grodansparadis/zeus/datasheets/capacitors.jpg

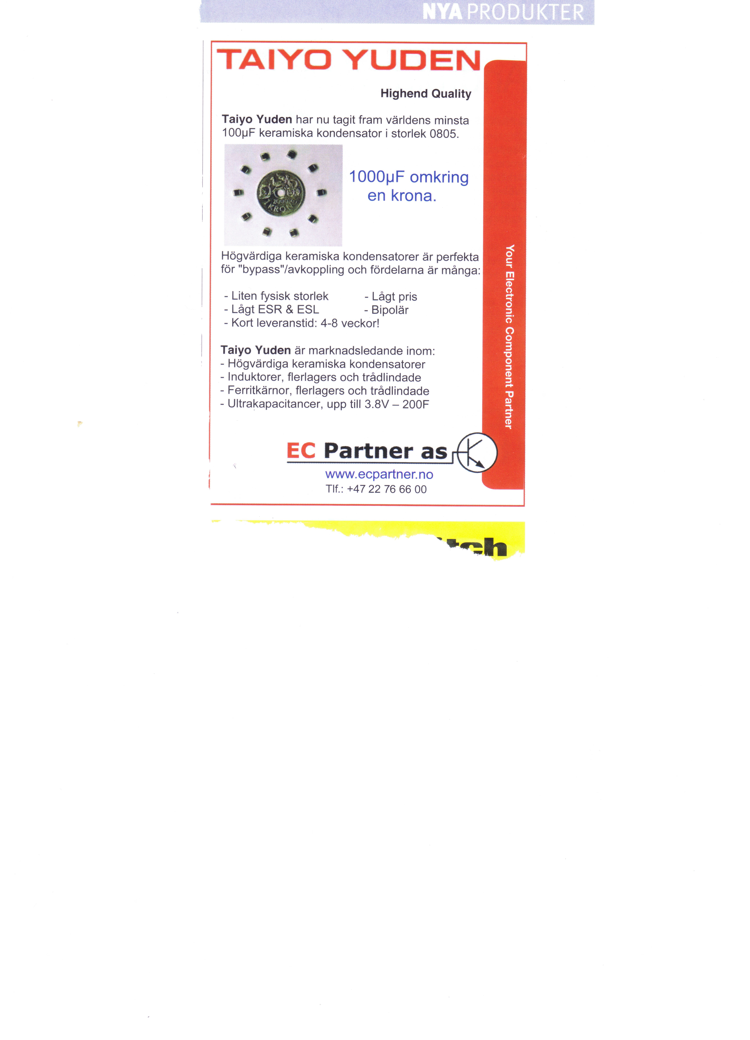
datasheets/capacitors.jpg
