grodansparadis/zeus/docs/547a1a08af27833d355dc69e661ba805.media.899x562.png

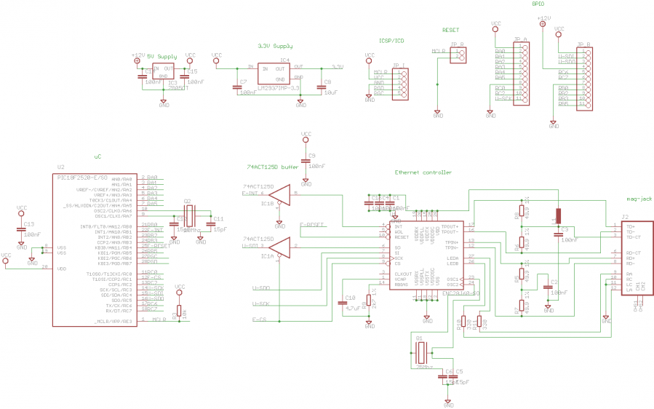
docs/547a1a08af27833d355dc69e661ba805.media.899x562.png
