grodansparadis/zeus/docs/AVR-WebServer-Rev.jpeg

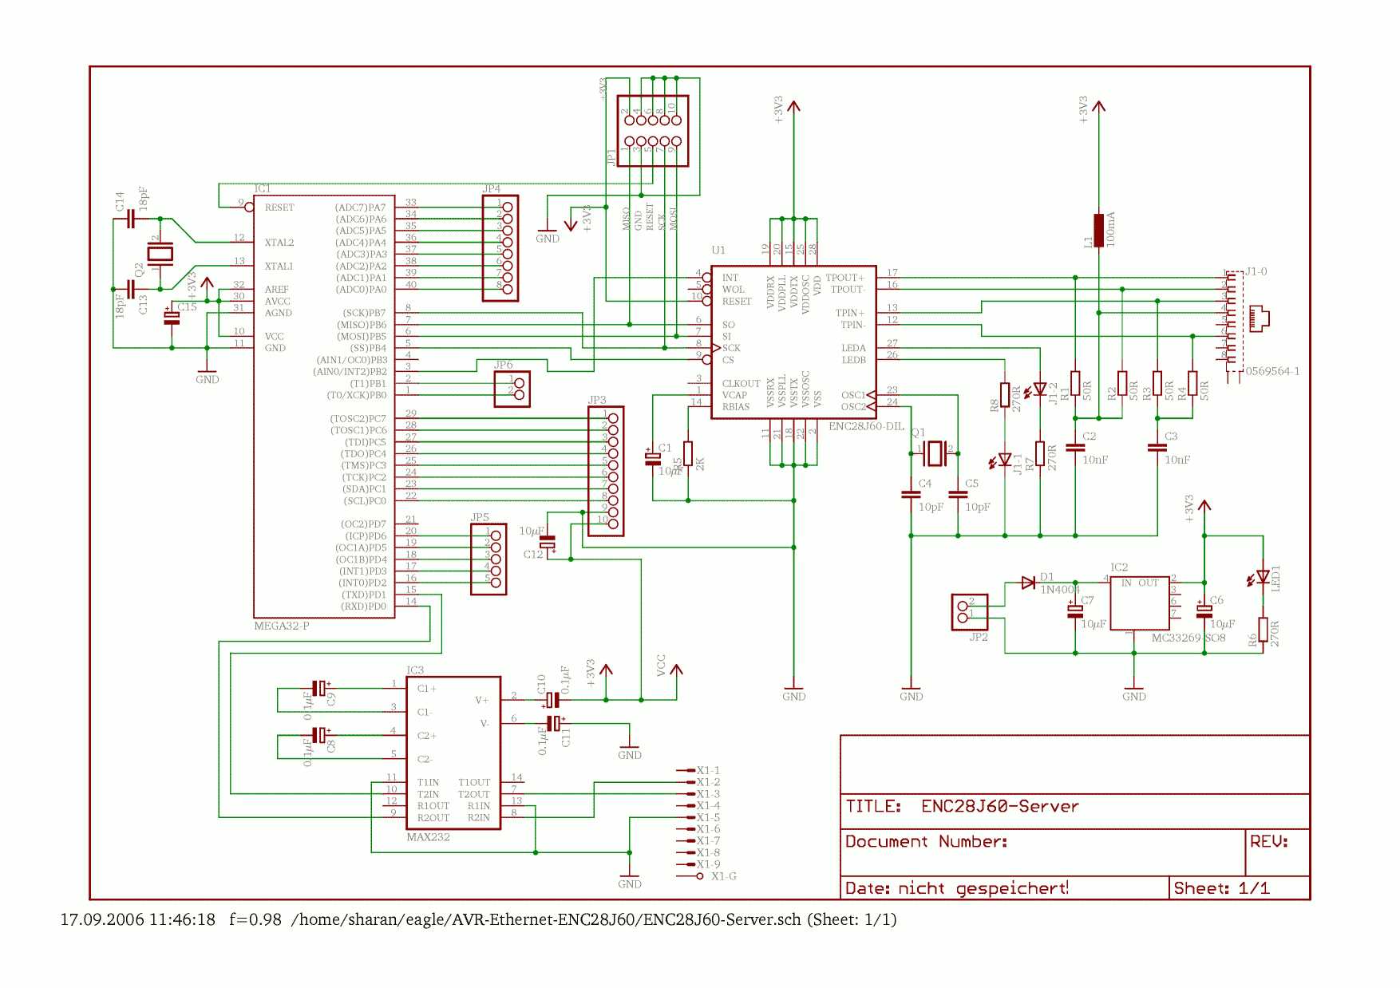
docs/AVR-WebServer-Rev.jpeg
