grodansparadis/zeus/docs/Magjack2.png

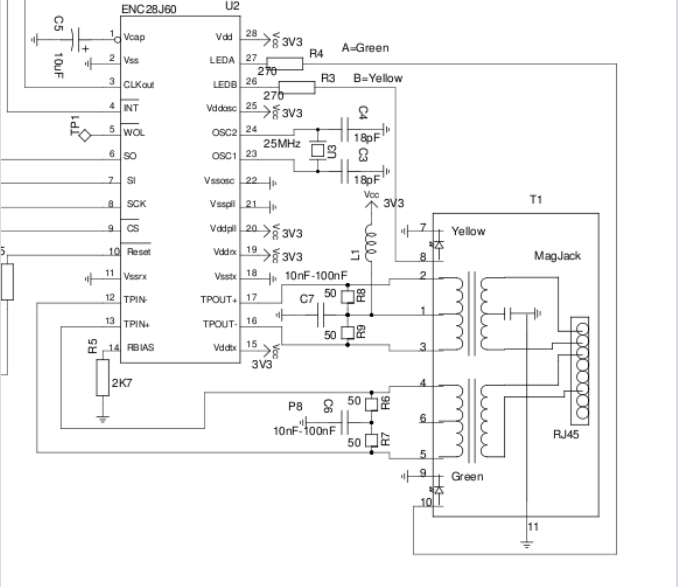
docs/Magjack2.png
