grodansparadis/zeus/docs/Magjack3.png

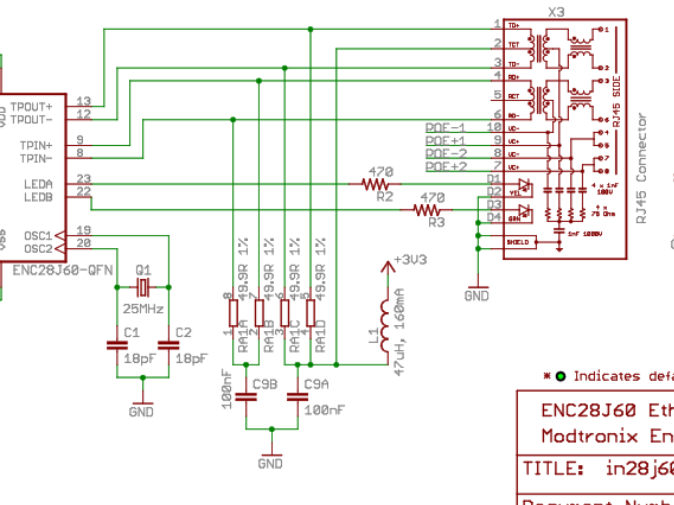
docs/Magjack3.png
