grodansparadis/zeus/docs/MOD-POE-PWR.gif

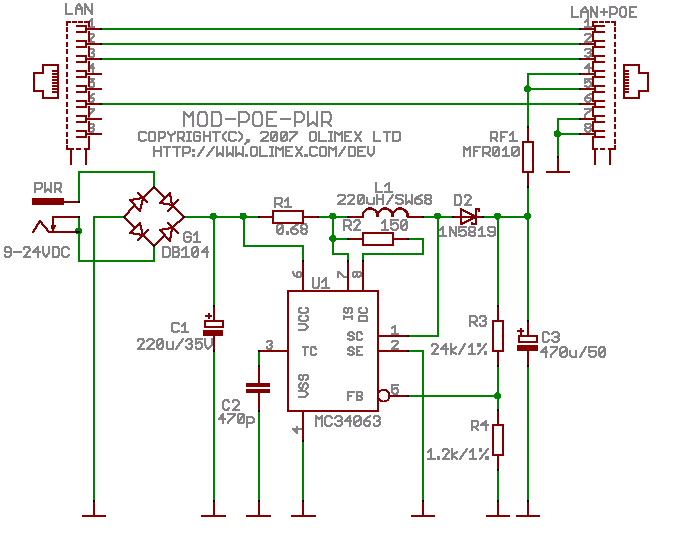
docs/MOD-POE-PWR.gif
