grodansparadis/zeus/docs/PIC-MAXI-WEB-REV-A-sch.gif

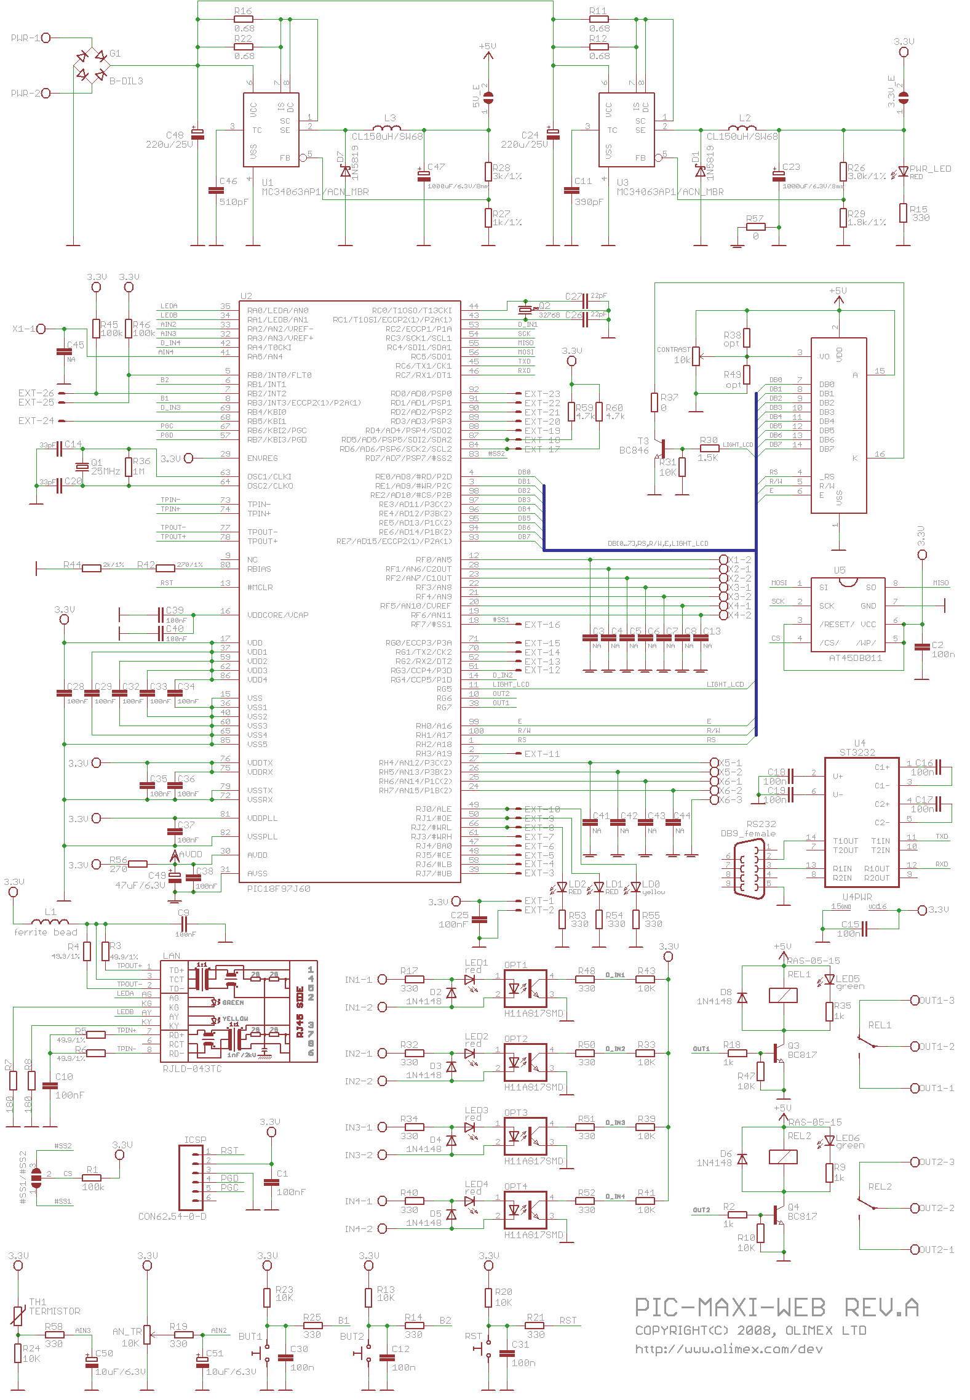
docs/PIC-MAXI-WEB-REV-A-sch.gif
