grodansparadis/zeus/docs/PIC-MICRO-WEB-sch.gif

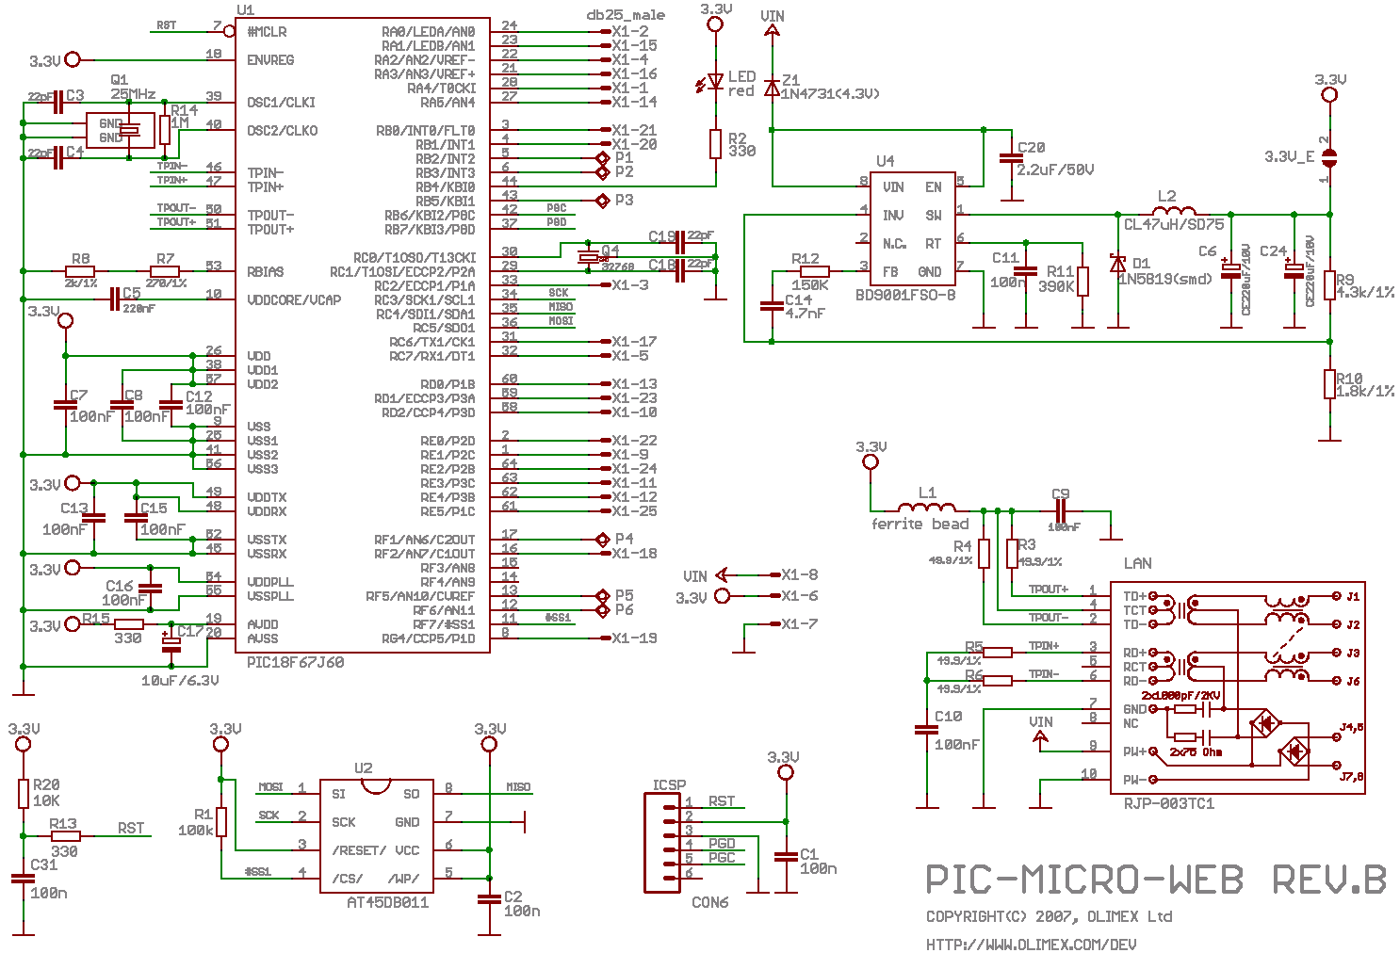
docs/PIC-MICRO-WEB-sch.gif
