grodansparadis/zeus/docs/railbox.png

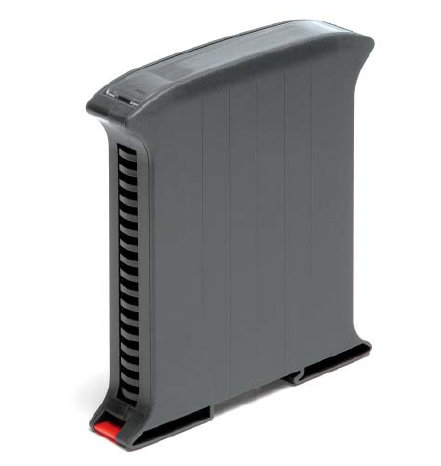
docs/railbox.png
