grodansparadis/zeus/docs/schaltplan.PNG

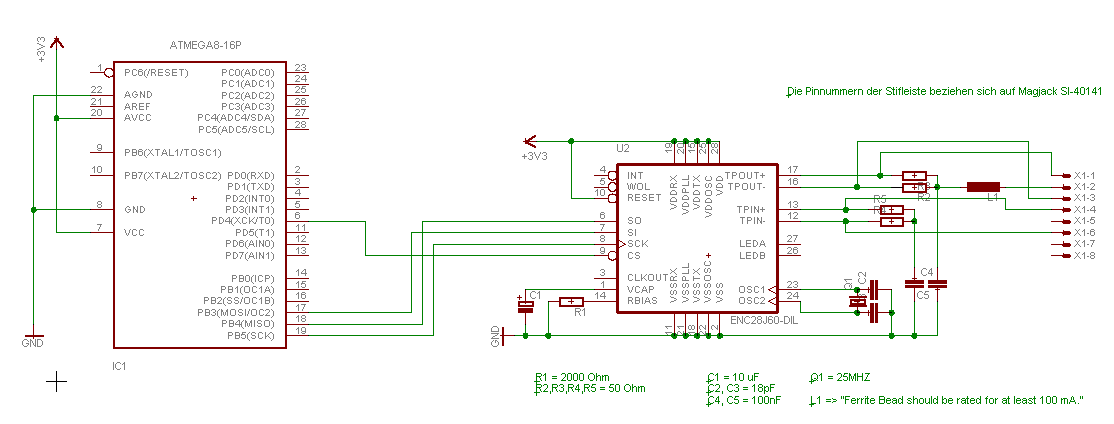
docs/schaltplan.PNG
