grodansparadis/zeus/eagle/expansion.png

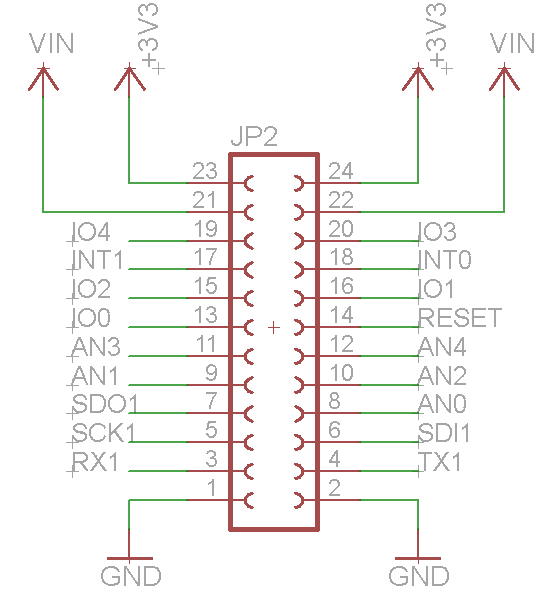
eagle/expansion.png
