grodansparadis/zeus/eagle/zeus_brd_rev_D.png

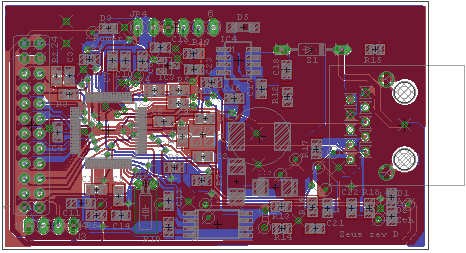
eagle/zeus_brd_rev_D.png
