grodansparadis/zeus/eagle/zeus_sch1_rev_D.png

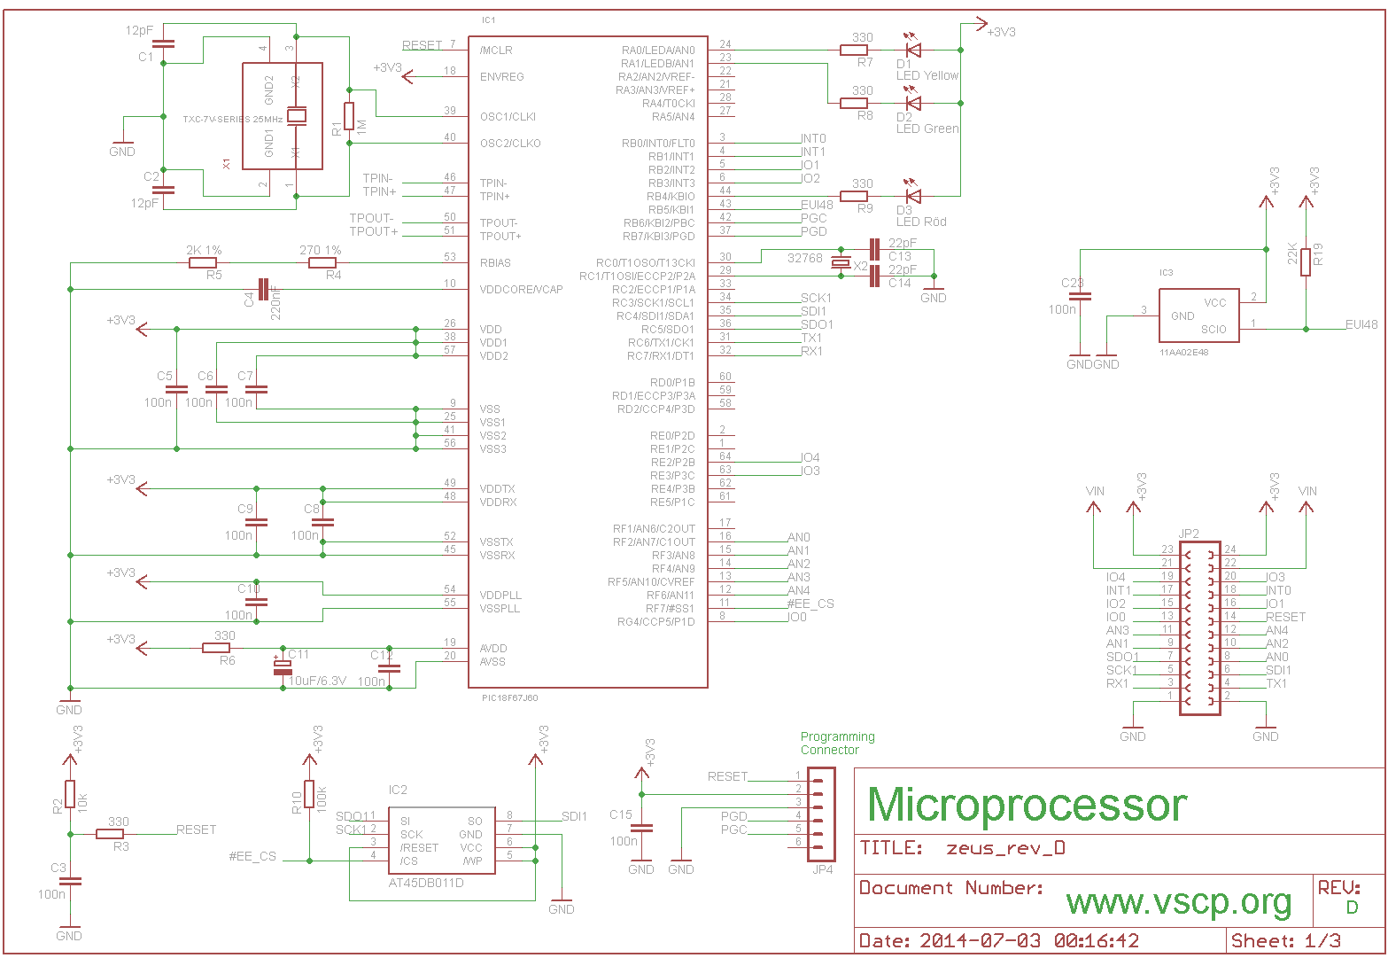
eagle/zeus_sch1_rev_D.png
