grodansparadis/zeus/eagle/zeus_sch2_rev_D.png

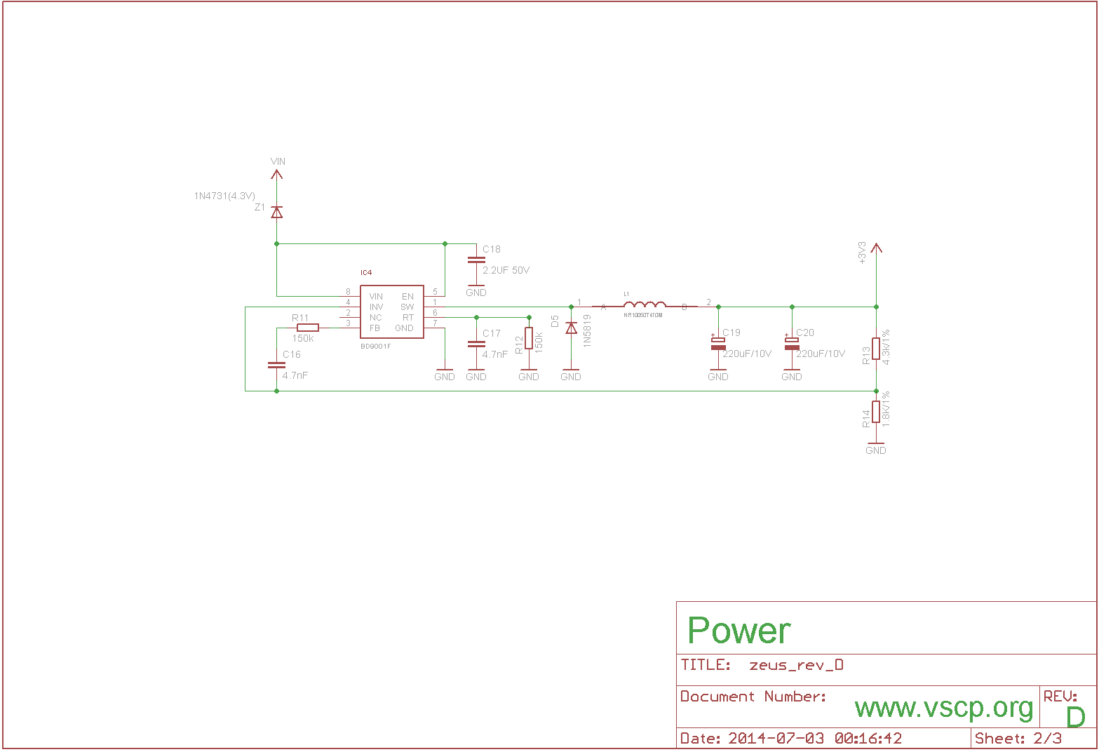
eagle/zeus_sch2_rev_D.png
