grodansparadis/zeus/eagle/zeus_sch3_rev_D.png

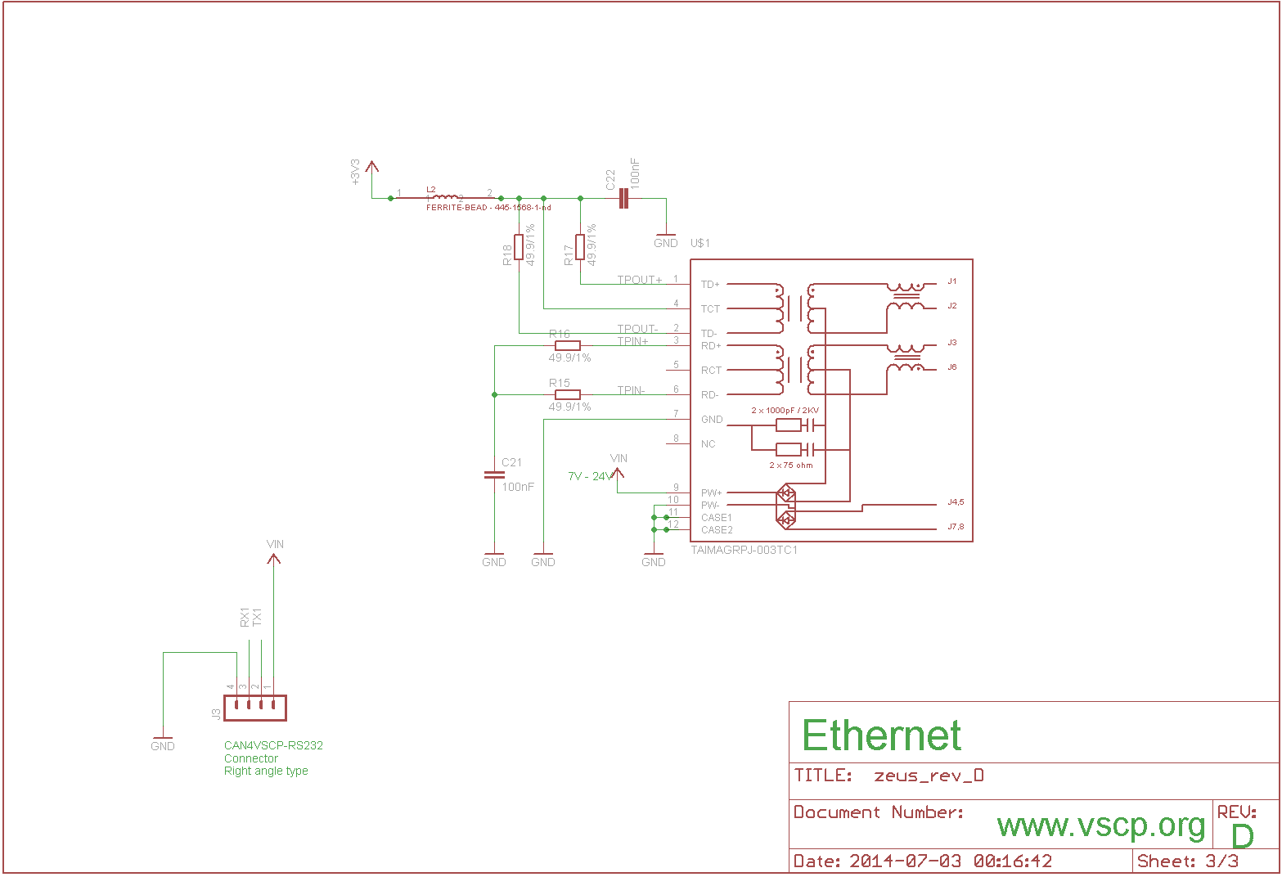
eagle/zeus_sch3_rev_D.png
