grodansparadis/zeus/docs/HY911103A.PDF

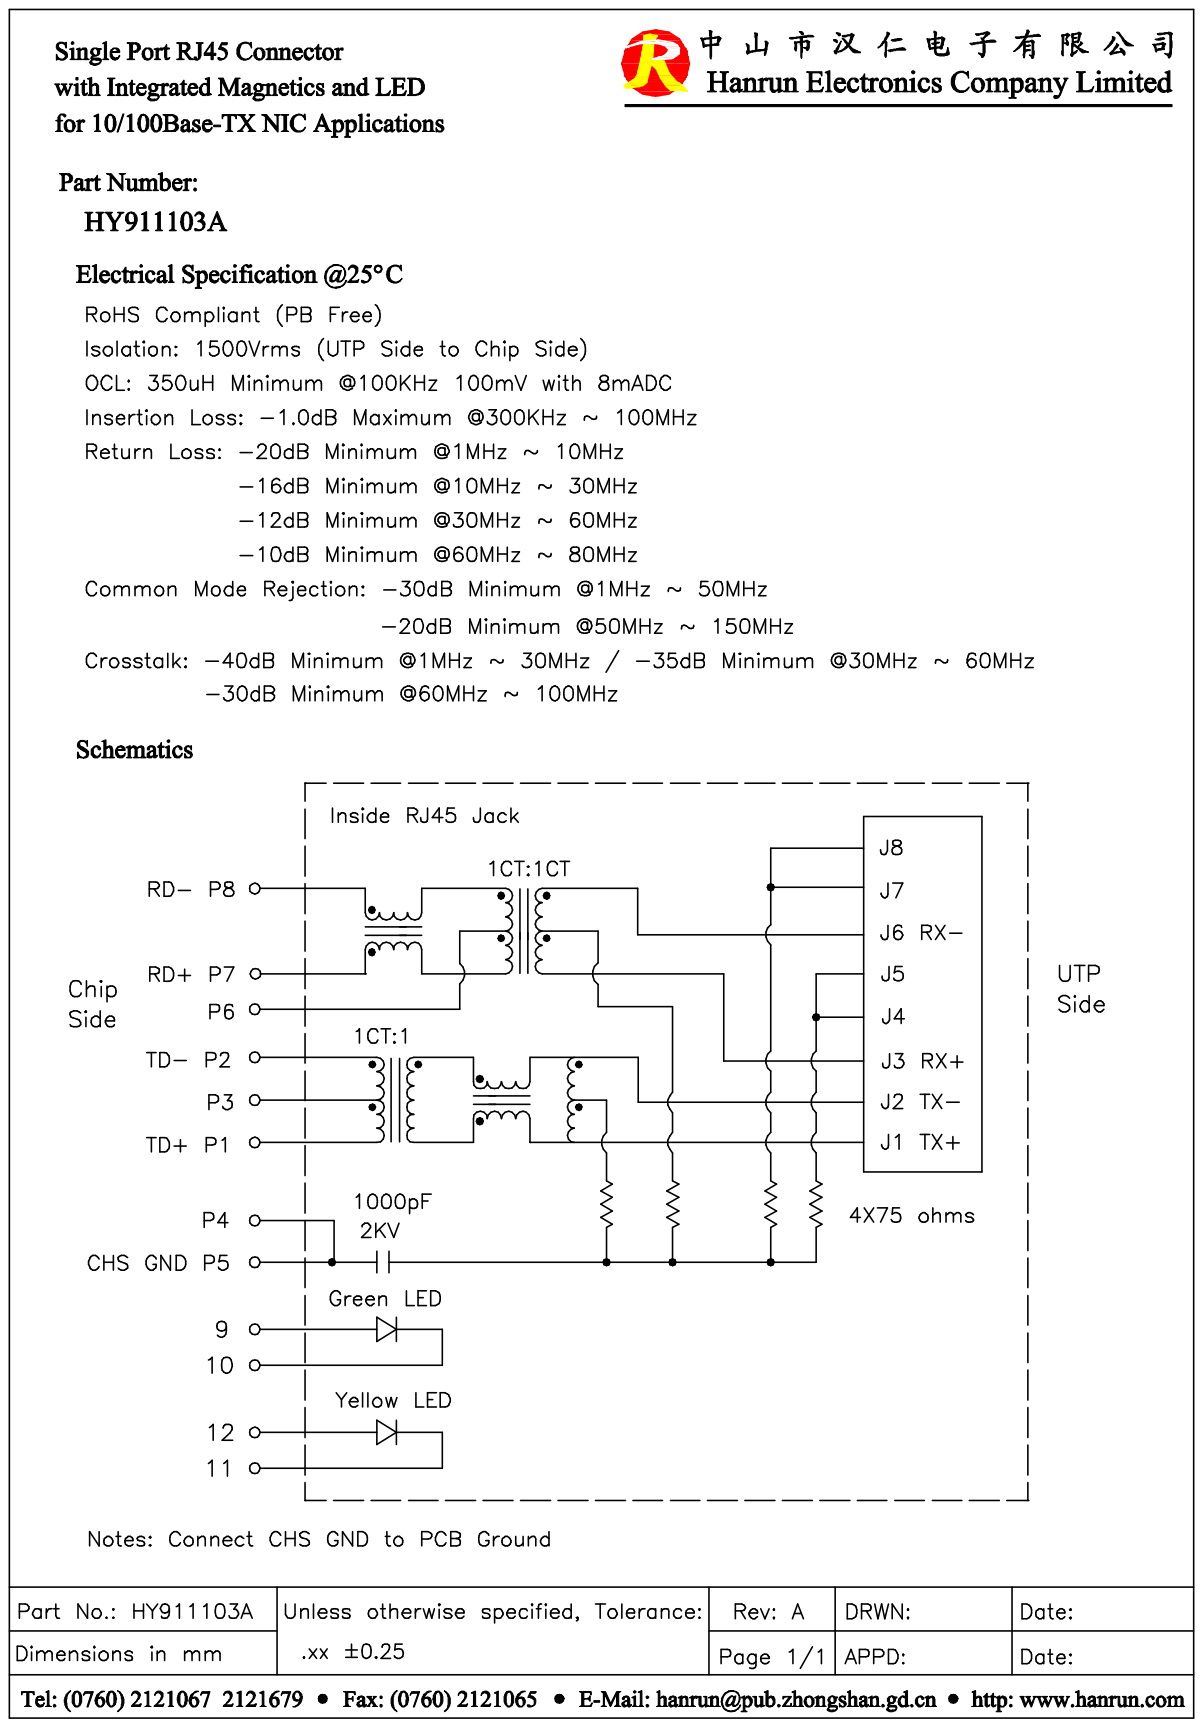
[picture p23: page 1]

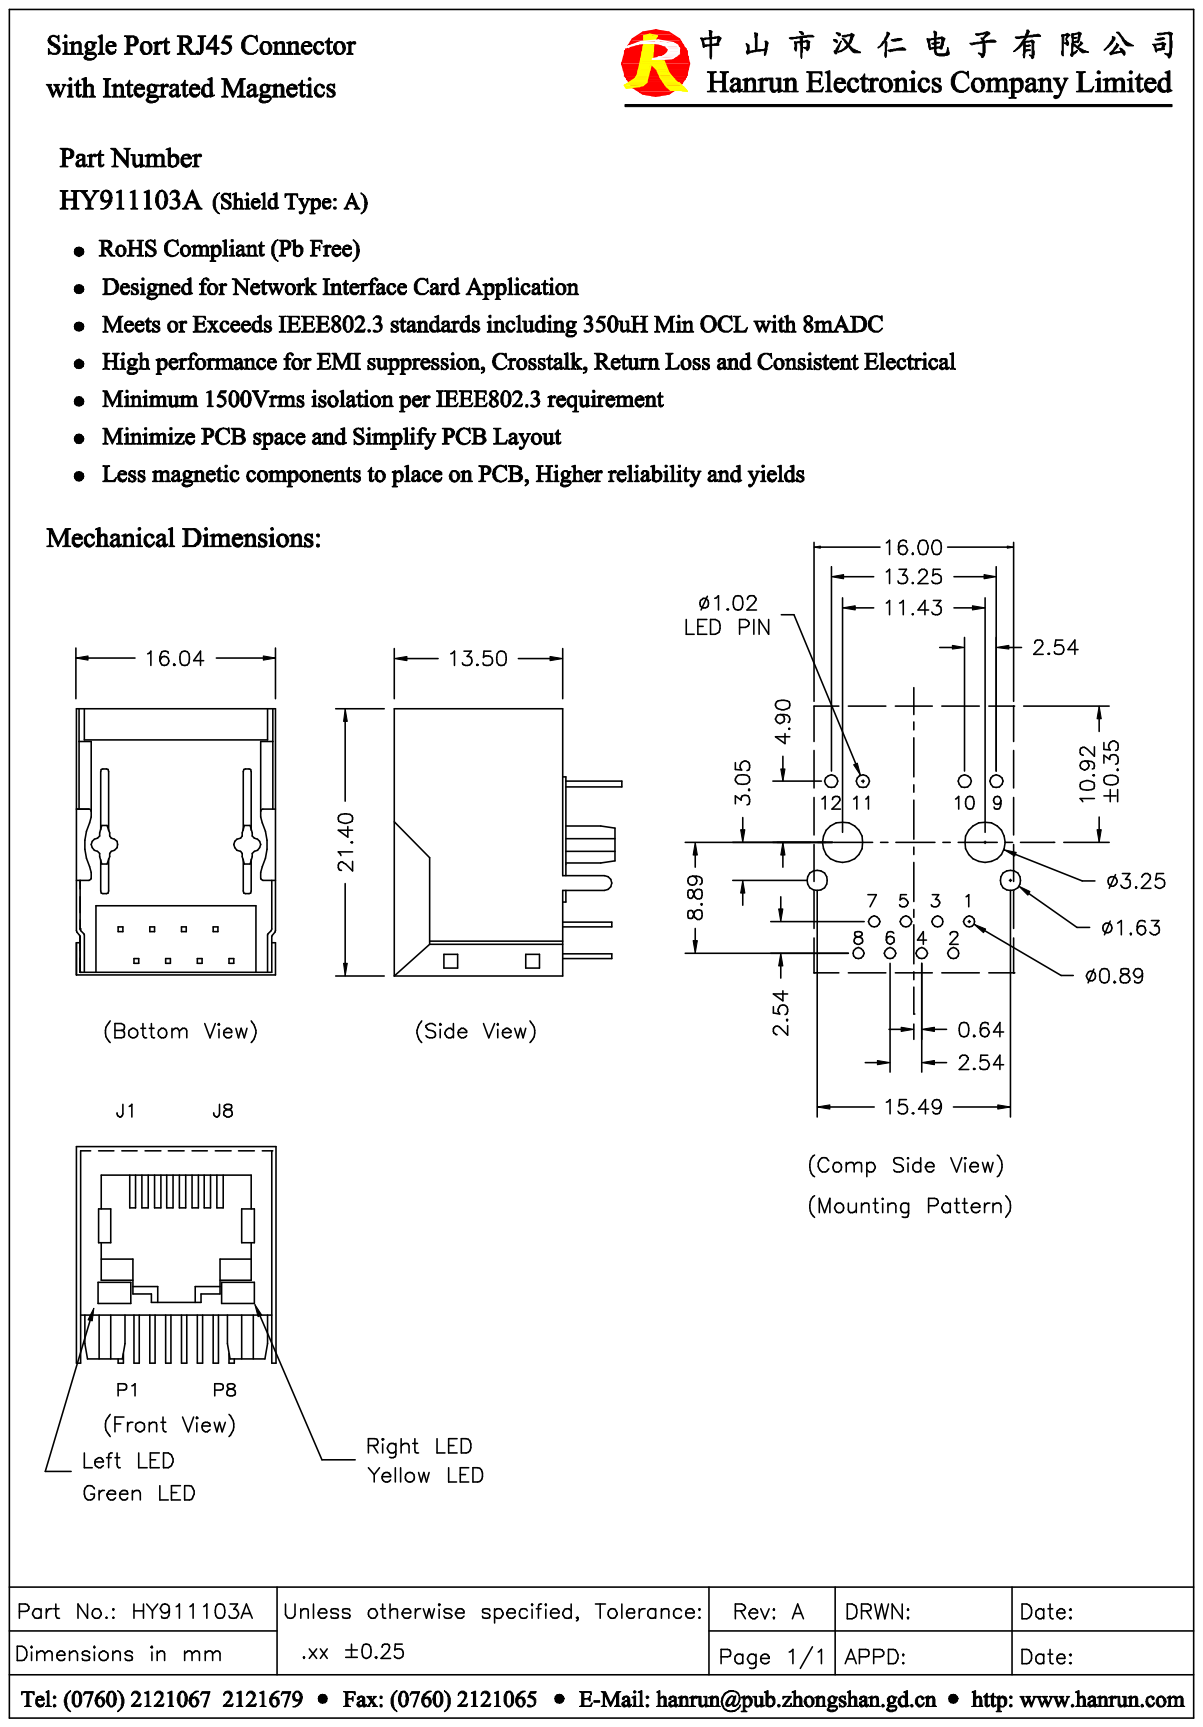
[picture p24: page 2]
