grodansparadis/zeus/docs/lancom.pdf

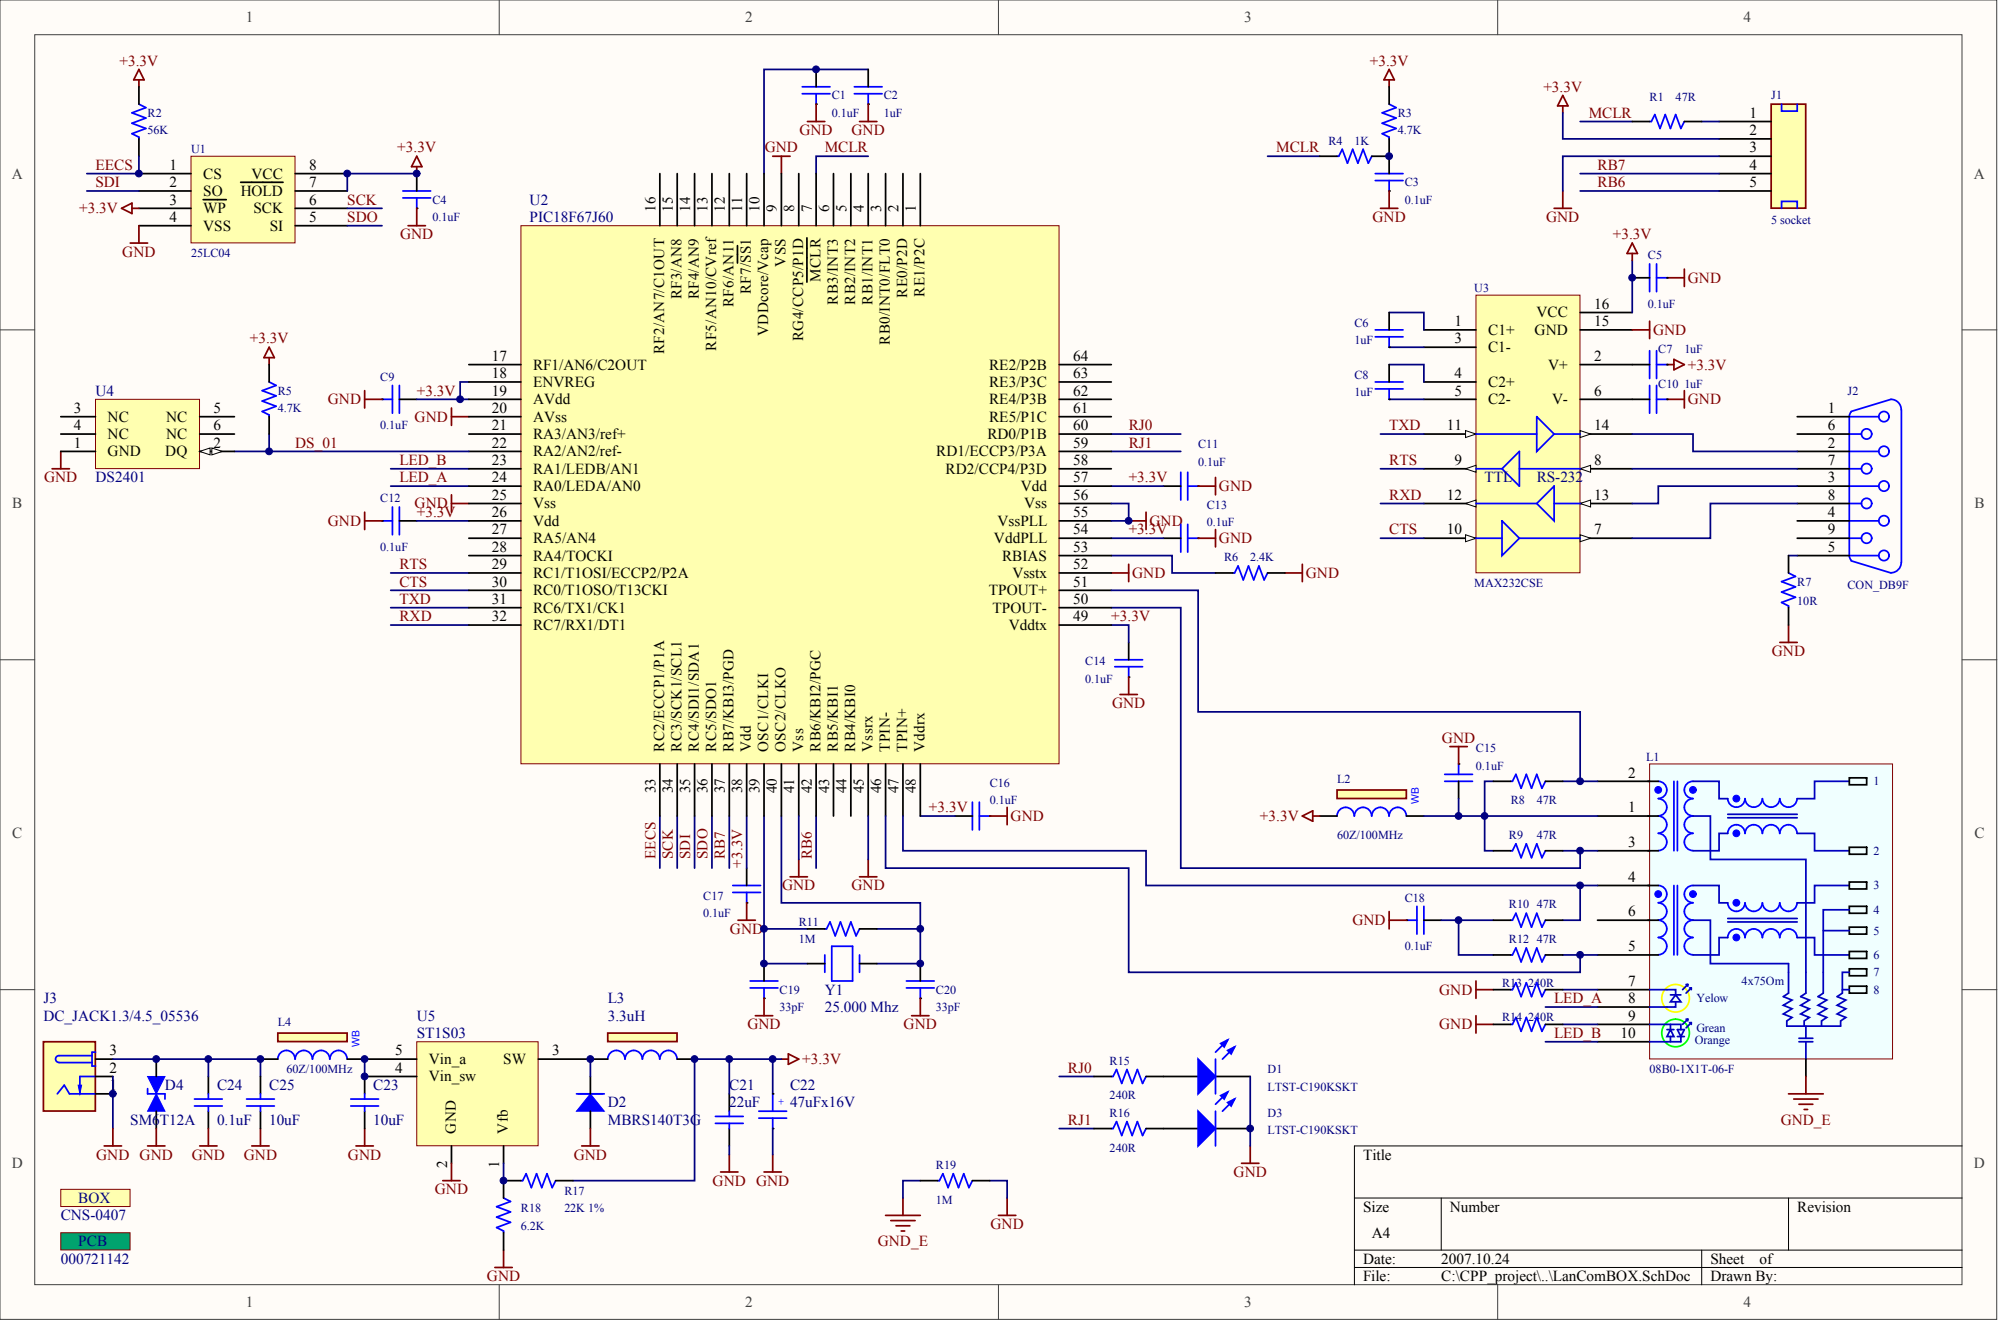
[picture p25: page 1]

RE1/P2C 1 RE0/P2D 2 RB0/INT0/FLT0 3 RB1/INT1 4 RB2/INT2 5 RB3/INT3 6 MCLR 7 RG4/CCP5/P1D 8 VSS 9 VDDcore/Vcap 10 RF7/SS1 11 RF6/AN11 12 RF5/AN10/CVref 13 RF4/AN9 14 RF3/AN8 15 RF2/AN7/C1OUT 16
