grodansparadis/zeus/docs/PIC-MICRO-WEB_demo_stack_5_31/Microchip/TCPIP Stack/SNMPv3.c

#include "TCPIPConfig.h"

#if defined(STACK_USE_SNMPV3_SERVER)
#include "TCPIP Stack/StackTsk.h"
#include "TCPIP Stack/SNMPv3.h"
#include "TCPIP Stack/Tick.h"
#include "TCPIP Stack/UDP.h"


typedef struct 
{
	UINT8 privAndAuthFlag:2;
    UINT8 reportableFlag :1;
}snmpV3MsgFlagsBitWise;


/*   
SNMP_ENGINE_MAX_MSG_SIZE is determined as the minimum of the max msg size
values supported among all of the transports available to and supported by the engine. 
*/
#define SNMP_ENGINE_MAX_MSG_SIZE	1024 
#define SET_SNMPV3_GET_PDU_INDEX  (gSNMPv3ScopedPduRequestBuf.length++)


/*header+MSGID +msgMAXSIZE +msg flag +security model */
#define MSGGLOBAL_HEADER_LEN(x)	( x= (2 \
							  +1+1+4 \
							  +1+1+4 \
							  +1+1+1  \
							  +1+1+1)\
						    )
/*header+ engineID+ engine boot+ engine time+security name+authentication parameters
+privacy parameters*/
#define MSG_AUTHORITATIVE_HEADER_LEN(x)   ( x=(2+2 \
								     +1+1+snmpEngnIDLength \
								     +1+1+4 \
								     +1+1+4 \
								     +1+1+securityPrimitivesOfIncomingPdu.securityNameLength \
								     +1+1+snmpOutMsgAuthParamLen \
								     +1+1+snmpOutMsgPrivParamLen) \
								)


/* Snmp Engine Group */
UINT8 snmpEngineID[32]; //Reserving 32 bytes for the snmpEngineID as the octet string length can vary form 5 to 32 
UINT32 snmpEngineBoots;//The number of times that the SNMP engine has (re-)initialized itself since snmpEngineID was last configured.
DWORD_VAL snmpEngineTime;//The number of seconds since the value of the snmpEngineBoots object last changed
DWORD_VAL snmpEngineMaxMessageSize;


UINT8 snmpEngnIDLength=0;
DWORD snmpEngineTimeOffset=0;
DWORD_VAL authoritativeSnmpEngineBoots;
DWORD_VAL authoritativeSnmpEngineTime;

UINT8 snmpInMsgAuthParamStrng[12];
UINT8 snmpInMsgAuthParamLen=12;
UINT8 snmpInMsgPrvParamStrng[8];
UINT8 snmpInMsgPrivParamLen=8;

UINT8 snmpOutMsgAuthParamStrng[12];
UINT8 snmpOutMsgAuthParamLen=12;
UINT8 snmpOutMsgPrvParamStrng[8];
UINT8 snmpOutMsgPrivParamLen=8;

UINT16 snmpMsgBufSeekPos=0;
UINT16 gSNMPv3ScopedPduDataPos=0;
WORD gSnmpv3UserDBIndex=0; 
WORD_VAL gUsmStatsEngineID={0}; 	

UINT32 snmpEngineSecurityModel=0;//Maximum range (2^31-1), RFC3411    ///done
UINT32 snmpEngineMsgProcessModel=0;//Maximum range (2^31-1), RFC3411 ///done
UINT8  snmpSecurityLevel=0; 
UINT8  snmpResponseSecurityFlag=0;

DWORD_VAL incomingSnmpPDUmsgID;
struct dispatcherProcessPdu incomingPdu;
SecuritySysProcessIncomingMsg securityPrimitivesOfIncomingPdu;

extern APP_CONFIG AppConfig;
extern void SaveAppConfig(void);
extern WORD SNMPTxOffset;
extern WORD msgSecrtyParamLenOffset;

SNMPV3MSGDATA gSNMPv3ScopedPduRequestBuf ={NULL,0,0,0};
SNMPV3MSGDATA gSNMPv3ScopedPduResponseBuf = {NULL,0,0,0};
SNMPV3MSGDATA gSNMPv3PduHeaderBuf = {NULL,0,0,0};
SNMPV3MSGDATA gSNMPv3TrapMsgHeaderBuf = {NULL,0,0,0};
SNMPV3MSGDATA gSNMPv3TrapScopedPduResponseBuf = {NULL,0,0,0};

SNMPV3_REQUEST_WHOLEMSG gSnmpV3InPduWholeMsgBuf={NULL,NULL,{0},{0},0,0,0,0};
SNMPV3_RESPONSE_WHOLEMSG gSnmpV3OUTPduWholeMsgBuf={NULL,NULL,{0},{0},0,0,0,0};
SNMPV3_RESPONSE_WHOLEMSG gSnmpV3TrapOUTPduWholeMsgBuf={NULL,NULL,{0},{0},0,0,0,0};


#if defined(SNMP_V1_V2_TRAP_WITH_SNMPV3)
//snmv3 global database for trap table
snmpV3TrapConfigDataBase gSnmpv3TrapConfigData[SNMPV3_USM_MAX_USER]=
	{ \
	{"microchip",SNMPV3_MSG_PROCESSING_MODEL,SNMPV3_USM_SECURITY_MODEL,AUTH_PRIV}, \
	{"SnmpAdmin",SNMPV3_MSG_PROCESSING_MODEL,SNMPV3_USM_SECURITY_MODEL,AUTH_NO_PRIV}, \
	{"root",SNMPV3_MSG_PROCESSING_MODEL,SNMPV3_USM_SECURITY_MODEL,NO_AUTH_NO_PRIV} \
	};
#endif

BOOL Snmpv3IsValidInt(DWORD* val);
BOOL IsSNMPv3ValidStructure(WORD* dataLen);
static BYTE FindOIDsFromSnmpV3Request(WORD pdulen);

void Snmpv3ReportPdu(SNMPV3MSGDATA *dynScopedBufPtr);
void Snmpv3FreeDynAllocMem(void);
static BOOL IsSnmpv3ValidOID(BYTE* oid, BYTE* len);
static BOOL IsSnmpV3ASNNull(void);
void Snmpv3SetErrorStatus(WORD errorStatusOffset,
                           WORD errorIndexOffset,
                           SNMP_ERR_STATUS errorStatus,
                           BYTE errorIndex,SNMPV3MSGDATA *dynScopedPduPutBuf);
BYTE Snmpv3IsValidAuthStructure(WORD* dataLen);
BOOL _Snmpv3IsValidInt(UINT8* wholeMsgPtr,WORD* pos, DWORD* val );
BOOL _IsSNMPv3ValidStructure(UINT8* wholeMsgPtr,WORD* pos, WORD* dataLen );
BYTE _Snmpv3IsValidAuthStructure(WORD* dataLen);



/****************************************************************************
  Function:
	UINT8 snmpConfigureEngineSecurityModel(UINT32 securityModelInRequest)
	
  Summary:
  	Updates the Snmp agent security model value.

  Description:
	Checks for the security model value the in the request pdu against the security 
	model value specified in the RFC3411 max range.
  	Updates the snmp agent global variable 'snmpEngineSecurityModel' for storing 
  	security model value reuqested in the incoming request from the SNMP managers.
	  	 		 		  	
  Precondition:
   	SNMPInit(); is called. The agent is recognised in the network as the SNMPv3 node.
   	Snmp request is received.
		
  Parameters:
  	securityModelInRequest : this value is populated from the incoming request PDUs.
  	
  Return Values:
	TRUE:	If the incoming PDU has valid security model value.
	FALSE:    If the incoming PDU has invalid or un supported security model.

  Remarks:
  	'snmpEngineSecurityModel' is value to uniquely identiy a security model of the 
  	security sub system whithin the SNMP management architecture. This value is 
  	used by the SNMP engine to send respond or inform PDUs to the other SNMP nodes.
  	'snmpEngineSecurityModel' value is used for interoperability. 
***************************************************************************/
UINT8 snmpConfigureEngineSecurityModel(UINT32 securityModelInRequest)
{
	if(securityModelInRequest < 0x80000000  )
	{
		
		if(securityModelInRequest > ANY_SECUTIRY_MODEL && 
		   securityModelInRequest <= SNMPV3_USM_SECURITY_MODEL
		   /* && User can add the Enterprise specific Security Model if reuired and is implemented */ )
		{
			snmpEngineSecurityModel=securityModelInRequest;
			return TRUE;
		}
		else
			return FALSE;
	}
	else
		return FALSE;
}


/****************************************************************************
  Function:
	UINT8 snmpEngineDecodeMessageFlags(UINT8 msgFlasgInRequest)
	
  Summary:
  	Returns the message flag value in the received incoming snmp request pdu. 

  Description:
	Compare the message flag value the in the request pdu against the Octet's 
	least significant three bits: Reportable, PrivFlag, AuthFlag. Return the message flag
	value to message processing model to take corresponding decision for the 
	message processing flow.  
		  	 		 		  	
  Precondition:
   	SNMPInit(); is called. The agent is recognised in the network as the SNMPv3 node.
	Snmp request is received.	

  Parameters:
  	'msgFlasgInRequest' is value populated from the incoming request PDUs.
  	
  Return Values:
	INVALID_MSG: If the incoming PDU has undefined message flag value  or 
	REPORT_FLAG_AND_SECURITY_LEVEL_FLAGS: if not INVALID_MSG, then 
	any other matching value in the enum except INVALID_MSG.

  Remarks:
  	'msgFlasgInRequest' is compared to possible combinations of snmp message flags.
  	The return value from this routine is utilised by the message processing unit to 
  	decide on the course of action to be taken while processing the incoming request. 
***************************************************************************/

UINT8 snmpEngineDecodeMessageFlags(UINT8 msgFlasgInRequest)
{
	if(msgFlasgInRequest > REPORT2REQ_PRIVACY_AND_AUTH_PROVIDED) /*if all msgFlags are SET*/
	{
		return INVALID_MSG;
	}
	else if( (msgFlasgInRequest & NO_REPORT_NO_PRIVACY_NO_AUTH) == NO_REPORT_NO_PRIVACY_NO_AUTH)
	{
		return NO_REPORT_NO_PRIVACY_NO_AUTH;
	}
	else if( (msgFlasgInRequest & NO_REPORT_NO_PRIVACY_BUT_AUTH_PROVIDED) == NO_REPORT_NO_PRIVACY_BUT_AUTH_PROVIDED)
	{
		return NO_REPORT_NO_PRIVACY_BUT_AUTH_PROVIDED;
	}
	else if( (msgFlasgInRequest & NO_REPORT_PRIVACY_PROVIDED_BUT_NO_AUTH) == NO_REPORT_PRIVACY_PROVIDED_BUT_NO_AUTH)
	{
		return INVALID_MSG;
	}
	else if( (msgFlasgInRequest & NO_REPORT_PRIVACY_AND_AUTH_PROVIDED) == NO_REPORT_PRIVACY_AND_AUTH_PROVIDED)
	{
		return NO_REPORT_PRIVACY_AND_AUTH_PROVIDED;
	}

	else if( (msgFlasgInRequest & REPORT2REQ_NO_PRIVACY_NO_AUTH) == REPORT2REQ_NO_PRIVACY_NO_AUTH)
	{
		return REPORT2REQ_NO_PRIVACY_NO_AUTH;
	}
	else if( (msgFlasgInRequest & REPORT2REQ_NO_PRIVACY_BUT_AUTH_PROVIDED) == REPORT2REQ_NO_PRIVACY_BUT_AUTH_PROVIDED)
	{
		return REPORT2REQ_NO_PRIVACY_BUT_AUTH_PROVIDED;
	}
	else if( (msgFlasgInRequest & REPORT2REQ_PRIVACY_PROVIDED_BUT_NO_AUTH) == REPORT2REQ_PRIVACY_PROVIDED_BUT_NO_AUTH)
	{
		return INVALID_MSG;
	}
	else if( (msgFlasgInRequest & REPORT2REQ_PRIVACY_AND_AUTH_PROVIDED) == REPORT2REQ_PRIVACY_AND_AUTH_PROVIDED)
	{
		return REPORT2REQ_PRIVACY_AND_AUTH_PROVIDED;
	}
	else
		return INVALID_MSG;
}



/****************************************************************************
  Function:
	DWORD Snmpv3TrackAuthEngineTimeTick(void)
	
  Summary:
  	Returns the internal tick timer value to be used by 'snmpEngineTime'.
	
  Description:
  	This routine reads the internal tick timer 48 bits, converts to seconds.
  	
  Precondition:
   	None

  Parameters:
  	None
  	
  Return Values:
	timeStamp : DWORD value of the timer ticks 

  Remarks:
	None
***************************************************************************/
DWORD Snmpv3TrackAuthEngineTimeTick(void)
{

	DWORD_VAL dwvHigh, dwvLow;
    DWORD dw;
    DWORD timeStamp;

	
	//TimeStamp
	// Get all 48 bits of the internal Tick timer
    do
   	{
	   	dwvHigh.Val = TickGetDiv64K();
	   	dwvLow.Val = TickGet();
	} while(dwvHigh.w[0] != dwvLow.w[1]);
    dwvHigh.Val = dwvHigh.w[1];
    
	// Find total contribution from lower DWORD
    dw = dwvLow.Val/(DWORD)TICK_SECOND;
    timeStamp = dw*100ul;
    dw = (dwvLow.Val - dw*(DWORD)TICK_SECOND)*100ul;		// Find fractional seconds and convert to 10ms ticks
    timeStamp += (dw+((DWORD)TICK_SECOND/2ul))/(DWORD)TICK_SECOND;

	// Itteratively add in the contribution from upper WORD
	while(dwvHigh.Val >= 0x1000ul)
	{
		timeStamp += (0x100000000000ull*100ull+(TICK_SECOND/2ull))/TICK_SECOND;
		dwvHigh.Val -= 0x1000;
	}	
	while(dwvHigh.Val >= 0x100ul)
	{
		timeStamp += (0x010000000000ull*100ull+(TICK_SECOND/2ull))/TICK_SECOND;
		dwvHigh.Val -= 0x100;
	}	
	while(dwvHigh.Val >= 0x10ul)
	{
		timeStamp += (0x001000000000ull*100ull+(TICK_SECOND/2ull))/TICK_SECOND;
		dwvHigh.Val -= 0x10;
	}	
	while(dwvHigh.Val)
	{
		timeStamp += (0x000100000000ull*100ull+(TICK_SECOND/2ull))/TICK_SECOND;
		dwvHigh.Val--;
	}
    
	return timeStamp;
}


/****************************************************************************
  Function:
	void Snmpv3FormulateEngineID(UINT8 fifthOctectIdentifier )
	
  Summary:
  	Formulates the snmpEngineID for the SNMPV3 engine.

  Description:
  	Formulates the snmpEngineID depending on value of  'fifthOctectIdentifier'.
	as MAC_ADDR_ENGN_ID using the application MAC address. 
  	'fifthOctectIdentifier' defualt set to MAC_ADDR_ENGN_ID as the following octets 
  	used for the snmpEngineID are of mac address.

	User can set this octet of their choice to fomulate new snmpEngineID.
	fifthOctectIdentifier=IPV4_ADDR_ENGN_ID; 
	
	If 
	fifthOctectIdentifier=ADMIN_ASSIGNED_TEXT;  or
	fifthOctectIdentifier=ADMIN_ASSIGNED_OCTETS;
	then the following octets should be provided by the administrator through some 
	custom application interface mechanism.
	API parameter 'fifthOctectIdentifier' has to be upated in the intefrace API before 
	passing through Snmpv3FormulateEngineID().  
  	 		 		  	
  Precondition:
   	InitAppConfig(); is called. 
		
  Parameters:
  	fifthOctectIdentifier : Value of the 5th octet in the snmpEngineID which indicates 
  	how the rest (6th and following octets) are formatted.
  	
  Return Values:
	None

  Remarks:
	Authentication and encryption keys are generated using corresponding passwords and 
	snmpEngineID. If the snmpEngineID is newly configured, then the auth and privacy keys 
	would also change. Hence while using this API to change the snmpEngineID dynamically,
	care should be taken to update the new localized keys at the agent as well as at the manager.
***************************************************************************/
void Snmpv3FormulateEngineID(UINT8 fifthOctectIdentifier )
{

UINT8* dummyptr;
UINT i;

//Modify this private enterprise assigned number to your organization number asssigned by IANA 
UINT32_VAL mchpPvtEntpriseAssignedNumber; 

mchpPvtEntpriseAssignedNumber.Val = 0x42C7; //microchip = 17095.


	//Set the first bit as '1b' .  Refer to RFC3411 section5 Page# 41	
	mchpPvtEntpriseAssignedNumber.Val = ((0x80000000) | mchpPvtEntpriseAssignedNumber.Val);

	snmpEngineID[0]=mchpPvtEntpriseAssignedNumber.v[3];
	snmpEngineID[1]=mchpPvtEntpriseAssignedNumber.v[2];
	snmpEngineID[2]=mchpPvtEntpriseAssignedNumber.v[1];
	snmpEngineID[3]=mchpPvtEntpriseAssignedNumber.v[0];

	//Refer to RFC3411 section5 Page# 41	
	fifthOctectIdentifier=MAC_ADDR_ENGN_ID;
	
	snmpEngineID[4]= fifthOctectIdentifier;

	if(fifthOctectIdentifier == MAC_ADDR_ENGN_ID)
	{
		for(i=0;i<6/*sizeof(MAC_ADDR)*/;i++)
		{
			snmpEngineID[5+i]=AppConfig.MyMACAddr.v[i];
		}
		
		snmpEngineID[5+6/*sizeof(MAC_ADDR)*/]='\0';
		snmpEngnIDLength=4/* 4 Bytes of IANA Pvt Enterprise Assigned Number*/
						+1/* 1 Byte for fifthOctectIdentifier*/
						+6/*sizeof(MAC_ADDR)*/;
	}
	else if(fifthOctectIdentifier == IPV4_ADDR_ENGN_ID)
	{
		dummyptr= (UINT8*)strncpy((char *)&snmpEngineID[5], (const char *) &AppConfig.MyMACAddr, sizeof(IP_ADDR));
	
		snmpEngineID[5+4/*sizeof(IP_ADDR)*/]='\0';
		snmpEngnIDLength=4/* 4 Bytes of IANA Pvt Enterprise Assigned Number*/
						+1/* 1 Byte for fifthOctectIdentifier*/
						+4 /*sizeof(IP_ADDR)*/;
	}
	else if((fifthOctectIdentifier == ADMIN_ASSIGNED_TEXT )||(fifthOctectIdentifier == ADMIN_ASSIGNED_OCTETS))
	{

		//Interface API updates the  snmpEngineID[4] = fifthOctectIdentifier 
		//and snmpEngineID[5] onwords with the corresponding octet string or value.
		;
		//snmpEngnIDLength=strlen((const char*) snmpEngineID);
	}
		
	
	//Increment the snmpEngineBoots record as snmpEngineID reconfigured
	snmpEngineBoots+=1;

	//Increment the snmpEngineBootRcrd to be stored in the non volatile memory 
	AppConfig.SnmpEngineBootRcrd=snmpEngineBoots;

	//Store the new incremented boot record to the non volatile memory
//	SaveAppConfig();

	//Reset the snmEngineTime as snmpEngineBoots incremented
	snmpEngineTime.Val=0;

	snmpEngineTimeOffset=Snmpv3TrackAuthEngineTimeTick();
}




/****************************************************************************
  Function:
	void Snmpv3MaintainEngineBootsRcrd(void)
	
  Summary:
  	Updates the snmp engine boots counter for the SNMPV3 engine.

  Description:
  	Updates the global snmpEngineBoots counter variable with the boots counter stored in the 
  	non volatile memory. Also increments and stores the new incremented value  to the non 
  	volatile memoryafter the SNMP engine initialization at the power cycle.
  	 		 		  	
  Precondition:
   	InitAppConfig(); is called.	

  Parameters:
  	None
  	
  Return Values:
	None

  Remarks:
	Should be called only during tcp/ip stack initialization and only after the InitAppConfig();
	is called.
***************************************************************************/
void Snmpv3MaintainEngineBootsRcrd(void)
{

	//Increment the snmpEngineBootRcrd as due to power cycle snmp egine reinitialization happened 
	//to be stored in the non volatile memory 
	AppConfig.SnmpEngineBootRcrd+=1;

	//Assgined this counter value to Global cntr which will track the snmp engine boot in real time.
	//'snmpEnigineBoots' can incremement in case of 'snmpEngineTime' overflow or adminstrator configuring  
	//'snmpEngineID' with new 'fifthOctectIdentifier' through administrative interface.
	snmpEngineBoots=AppConfig.SnmpEngineBootRcrd;

	//Store the new incremented boot record to the non volatile memory
	//SaveAppConfig();


}



/****************************************************************************
  Function:
	void Snmpv3GetAuthEngineTime(void)
	
  Summary:
  	Updates the snmp engine time variable 'snmpEngineTime' for the SNMPV3 engine. 
	
  Description:
  	'snmpEngineTime' is used for Timeliness checking for Message level security. Snmp 
  	engine keep updating the ''snmpEngineTime' variable for checking the time window 
  	for the requrest and responses/inform etc. This routine also updates snmpEngineBoots
  	in scenarios of internal timer reset or 'snmpEngineTime' cntr ovrflowed 
  	the (2^31 -1) value specified in RFC3411. 
  	 		 		  	
  Precondition:
   	SNMPInit(); is called.	

  Parameters:
  	None
  	
  Return Values:
	None

  Remarks:
	This routine is called every time the rx/tx PDU processing is handled  by the SNMP agent.
	Updates the 'snmpEngineTime' and requires frequnet access to internal timer registers. 
***************************************************************************/
void Snmpv3GetAuthEngineTime(void)
{
	snmpEngineTime.Val=Snmpv3TrackAuthEngineTimeTick()-snmpEngineTimeOffset;

	if((Snmpv3TrackAuthEngineTimeTick() < snmpEngineTimeOffset)/* Internal Timer Reset occured*/
	   ||(snmpEngineTime.Val > 2147483647 /* (2^31 -1) Refer RFC 3411 Section 5 */))
	{
		/*This means the snmpEngineTime cntr ovrflowed the (2^31 -1) value 
		    or the internal Tick timer Reset occured*/
		snmpEngineTime.Val=0;
		snmpEngineTimeOffset=0;

		//Increment the snmpEngineBoots counter
		Snmpv3MaintainEngineBootsRcrd();
		
	}


}




/****************************************************************************
  Function:
	UINT8 Snmpv3NegotiateEngineMaxMsgSize(UINT32 maxMsgSizeInRequest)
	
  Summary:
  	Snmp engine max pdu message size is updated for the pdu recipient from this
  	Snmp agent.
	
  Description:
  	This routine defines the maximum size PDU that could be generated or received 
  	from this SNMP agent. The maximum size is limited to the maximum pdu size the
  	recipient can receive and process or originator can sent. For this SNMP engine, 
  	maximum message size is limited between 484 and 'SNMP_ENGINE_MAX_MSG_SIZE'. 
   	SNMP_ENGINE_MAX_MSG_SIZE is determined as the minimum of the maximum 
   	message size values supported among all of the transports available to and supported 
   	by the engine. 
   	
   Precondition:
   	The SNMP engine should have received a message from the other Snmp node 
   	notifying the maximum message size they can receive and process or send. 
 

  Parameters:
  	maxMsgSizeInRequest: incoming SNMPv3 request max msg size value
  	
  Return Values:
	TRUE:  If the incoming message size is in the predefined range
	FALSE: If the incoming maximum messgae size is less than 484 bytes 

  Remarks:
	SNMP_ENGINE_MAX_MSG_SIZE should not be more than 0x80000000 (2^31 -1).
	
***************************************************************************/
UINT8 Snmpv3NegotiateEngineMaxMsgSize(UINT32 maxMsgSizeInRequest)
{

	snmpEngineMaxMessageSize.Val=SNMP_ENGINE_MAX_MSG_SIZE;//"The maximum length in octets of an SNMP message ranges 484 to (2^31-1), send or receive and process.RFC3411


	if(maxMsgSizeInRequest > 0x80000000 || maxMsgSizeInRequest< 484)

		return FALSE;

	else if(maxMsgSizeInRequest < SNMP_ENGINE_MAX_MSG_SIZE ) 
	{
		snmpEngineMaxMessageSize.Val=maxMsgSizeInRequest;
		return TRUE;
	}
	else
		snmpEngineMaxMessageSize.Val=SNMP_ENGINE_MAX_MSG_SIZE;
		return TRUE;
}


/****************************************************************************
  Function:
	BOOL Snmpv3BufferPut(BYTE val ,SNMPV3MSGDATA *putbuf)
	
  Summary:
  	Copies BYTE data to dynamically allocated memory buffer.

  Description:
	The SNMPv3 stack implementation uses dynamically allocated memory buffer for
	processing of request and response packets. This routine copies the BYTE data to the 
	allocated buffer and updates the offset length couter. 
		  	 		 		  	
  Precondition:
	The SNMPv3 stack has sucessfully allocated dynamic memory buffer from the Heap
   	
  Parameters:
  	val: BYTE value to be written to the buffer
  	putbuf: pointer to the dynamically allocated buffer to which the 'val' to be written 
  	
  Return Values:
	TRUE: if successfully write to the buffer
	FALSE: failure in writing to the buffer
	
  Remarks:
  	This routine is used by the SNMPv3 stack. If required to be used by the application
  	code, valid pointers should be passed to this routine. 
  	
***************************************************************************/
BOOL Snmpv3BufferPut(BYTE val ,SNMPV3MSGDATA *putbuf)
{
	if(putbuf->maxlength > putbuf->length)
	{
		putbuf->head[putbuf->length] = (BYTE)val;
		putbuf->length++;
		return TRUE;
	}
	else
	{
		return FALSE;
	}

}

/****************************************************************************
  Function:
	BOOL Snmpv3GetBufferData(SNMPV3MSGDATA getbuf,UINT16 pos)
	
  Summary:
  	Reads BYTE data from dynamically allocated memory buffer.

  Description:
	The SNMPv3 stack implementation uses dynamically allocated memory buffer for
	processing of request and response packets. This routine reads the BYTE data from 
	the allocated buffer at the positions (offset) provided.
		  	 		 		  	
  Precondition:
	The SNMPv3 stack has sucessfully allocated dynamic memory buffer from the Heap
   	
  Parameters:
  	getbuf: Structure from where to read the data byte.
  	pos: position in the buffer from which the data to be read 
  	
  Return Values:
	BYTE: 1 byte value read
	
  Remarks:
  	The read position offset is required to be provided every time the routine is called.
  	This API do not increment the buffer read offset automatically, everytime it is called. 
  	
***************************************************************************/	
BYTE Snmpv3GetBufferData(SNMPV3MSGDATA getbuf,UINT16 pos)
{
	return (BYTE)(getbuf.head[pos]);
}


/****************************************************************************
  Function:
	BYTE Snmpv3GetWholeMsgBufferData(UINT8* getbuf, UINT16* pos)
	
  Summary:
  	Reads BYTE data from dynamically allocated memory buffer.

  Description:
	The SNMPv3 stack implementation uses dynamically allocated memory buffer for
	processing of request and response packets. This routine reads the BYTE data from 
	the allocated buffer at the positions (offset) provided.
		  	 		 		  	
  Precondition:
	The SNMPv3 stack has sucessfully allocated dynamic memory buffer from the Heap
   	
  Parameters:
  	getbuf: pointer to the buffer where the request or repsonse data is stored.
  	pos: pointer to the position in the buffer from which the data to be read 
  	
  Return Values:
	BYTE: 1 byte value read
	
  Remarks:
  	This API increments the read offset every time it is called. Hence useful in the 
  	consecutive reads.  
  	
***************************************************************************/	
BYTE Snmpv3GetWholeMsgBufferData(UINT8* getbuf, UINT16* pos)
{
UINT8* testPtr;
UINT16* posPtr;

	posPtr=pos; 
	testPtr=getbuf+*posPtr;
	
	*pos=(*posPtr+1);
	return (BYTE)*(testPtr);
}


/****************************************************************************
  Function: 
  	SNMP_ACTION Snmpv3MsgProcessingModelProcessPDU(BYTE inOutPdu)

  Summary:
  	This routine collects or populates the message processing model infomation 
  	from the received SNMPv3 request PDU or to the response PDU respectively.
  
  Description:
	The recievd SNMPv3 PDU or the transmit PDU header has message processing
	data bytes infomration. This routine retrievs the messgae processing model 
	infomration from the stored pdu or write the appropriate msg proc info to the 
	repsonse msg buffer.
		  	 		 		  	
  Precondition:
	Valid SNMPv3 request msg is received.
   	
  Parameters:
  	inOutPdu: indicates whether the incomig PDU is to be read for msg proc values 
  	to be retrieved or the response PDU is to be populated with these values 
  	
  Return Values:
	SNMP_NO_CREATION: Failure due to improper msg processing information format in
					      the received PDU or failure in constructing the response PDU.
	SNMP_NO_ERR: The message processing infomration retrieval or response PDU 
				   fomration is successful
				   
  Remarks:
  	The messgae processing model parameters like 'msgID', 'msgMaxSize', 'msgFlags' and 
  	'msgSecurityModel' decides the SNMPv3 engine processing modalities regarding 
  	request or response PDU  	
***************************************************************************/
SNMP_ACTION Snmpv3MsgProcessingModelProcessPDU(BYTE inOutPdu)
{
	DWORD_VAL tempLen={0};
	BYTE tempData=0;	
	UINT8 *ptr=NULL;
	WORD tempPos=0,snmpv3Headerlength=0;
	BYTE snmpv3MsgGlobalHeaderlength=0;
	BYTE snmpv3MsgAuthHedaerLength = 0;	
	  
	if(inOutPdu == SNMP_REQUEST_PDU)
	{
		tempPos=snmpMsgBufSeekPos=0x00;
		if (!_IsSNMPv3ValidStructure(gSnmpV3InPduWholeMsgBuf.snmpMsgHead,&tempPos,(WORD*)&tempLen.w[0]))
			return SNMP_NO_CREATION;
		
		//Check and collect "msgID"
		if(! _Snmpv3IsValidInt(gSnmpV3InPduWholeMsgBuf.snmpMsgHead,&tempPos,&tempLen.Val))
			return SNMP_NO_CREATION;	

		incomingSnmpPDUmsgID.Val= tempLen.Val;

		//Check and collect "msgMaxSize" 
		if(! _Snmpv3IsValidInt(gSnmpV3InPduWholeMsgBuf.snmpMsgHead,&tempPos,&tempLen.Val))
			return SNMP_NO_CREATION;	
		
		incomingPdu.maxSizeResponseScopedPDU.Val = tempLen.Val;

		if(Snmpv3NegotiateEngineMaxMsgSize(tempLen.Val)==FALSE)
			return SNMP_NO_CREATION; 	

		//Check and collect "msgFlags" 
		tempData = Snmpv3GetWholeMsgBufferData(gSnmpV3InPduWholeMsgBuf.snmpMsgHead,&tempPos);
		
		if ( !IS_OCTET_STRING(tempData) )
			return FALSE;

		tempData=Snmpv3GetWholeMsgBufferData(gSnmpV3InPduWholeMsgBuf.snmpMsgHead,&tempPos);//Length byte of "msgFlags"
		tempData=Snmpv3GetWholeMsgBufferData(gSnmpV3InPduWholeMsgBuf.snmpMsgHead,&tempPos);//"msgFlag"

		snmpSecurityLevel=tempData;
		incomingPdu.securityLevel=snmpSecurityLevel;
		securityPrimitivesOfIncomingPdu.securityLevel=snmpSecurityLevel;

		//Check and collect "msgSecurityModel"	
		if(! _Snmpv3IsValidInt(gSnmpV3InPduWholeMsgBuf.snmpMsgHead,&tempPos,(DWORD*)&tempLen.Val))
			return SNMP_NO_CREATION;	

		if(snmpConfigureEngineSecurityModel(tempLen.Val))
		{
			incomingPdu.securityModel= tempLen.Val;
			securityPrimitivesOfIncomingPdu.securityModel= (BYTE)tempLen.Val;
		}
		else
			return SNMP_NO_CREATION;

		snmpMsgBufSeekPos=tempPos;	
	}
	else if(inOutPdu == SNMP_RESPONSE_PDU)
	{
		BOOL retBuf=TRUE;

		snmpv3Headerlength = MSGGLOBAL_HEADER_LEN(snmpv3MsgGlobalHeaderlength)+
							  MSG_AUTHORITATIVE_HEADER_LEN(snmpv3MsgAuthHedaerLength);

		ptr = gSNMPv3PduHeaderBuf.head = (UINT8 *)(malloc((size_t)snmpv3Headerlength+5));
		if(ptr == NULL)
			return SNMP_NO_CREATION;
		
		gSNMPv3PduHeaderBuf.length = 0;
		gSNMPv3PduHeaderBuf.maxlength = snmpv3Headerlength+1;

		//message header
		Snmpv3BufferPut(STRUCTURE,&gSNMPv3PduHeaderBuf);
		Snmpv3BufferPut(MSGGLOBAL_HEADER_LEN(snmpv3MsgGlobalHeaderlength)-2,&gSNMPv3PduHeaderBuf);

		//Put "msgID" type ASN_INT of length 4 bytes	
		Snmpv3BufferPut(ASN_INT,&gSNMPv3PduHeaderBuf);		
		Snmpv3BufferPut(0x04,&gSNMPv3PduHeaderBuf);
		Snmpv3BufferPut(incomingSnmpPDUmsgID.v[3],&gSNMPv3PduHeaderBuf);
		Snmpv3BufferPut(incomingSnmpPDUmsgID.v[2],&gSNMPv3PduHeaderBuf);
		Snmpv3BufferPut(incomingSnmpPDUmsgID.v[1],&gSNMPv3PduHeaderBuf);
		Snmpv3BufferPut(incomingSnmpPDUmsgID.v[0],&gSNMPv3PduHeaderBuf);

		//Put "msgMaxSize"  type ASN_INT of length 4 bytes
		Snmpv3BufferPut(ASN_INT,&gSNMPv3PduHeaderBuf);
		Snmpv3BufferPut(0x04,&gSNMPv3PduHeaderBuf);
		Snmpv3BufferPut(snmpEngineMaxMessageSize.v[3],&gSNMPv3PduHeaderBuf);
		Snmpv3BufferPut(snmpEngineMaxMessageSize.v[2],&gSNMPv3PduHeaderBuf);
		Snmpv3BufferPut(snmpEngineMaxMessageSize.v[1],&gSNMPv3PduHeaderBuf);
		Snmpv3BufferPut(snmpEngineMaxMessageSize.v[0],&gSNMPv3PduHeaderBuf);

		//Put "msgFlags"  type octet_string 
		Snmpv3BufferPut(OCTET_STRING,&gSNMPv3PduHeaderBuf);
		Snmpv3BufferPut(0x01,&gSNMPv3PduHeaderBuf);

		if((snmpSecurityLevel & 0x03)==0x03) // Rxed pkt is authenticated and encrypted
		{
			snmpResponseSecurityFlag=0x03;
			Snmpv3BufferPut(snmpResponseSecurityFlag,&gSNMPv3PduHeaderBuf);//Rsponse "msgFlags" value as Reportable, Encrypted and Authenticated Bits are not set. 
		}
		else if ((snmpSecurityLevel & 0x01)==0x01) // Rxed pkt is  authenticated and no priv
		{
			snmpResponseSecurityFlag=0x01;
			Snmpv3BufferPut(snmpResponseSecurityFlag,&gSNMPv3PduHeaderBuf);//Rsponse "msgFlags" value as Reportable, Encrypted and Authenticated Bits are not set. 
		}
		else
		{			
			snmpResponseSecurityFlag=0x00;
			Snmpv3BufferPut(snmpResponseSecurityFlag,&gSNMPv3PduHeaderBuf);
		}
		//Put "msgSecurityModel"	
		Snmpv3BufferPut(ASN_INT,&gSNMPv3PduHeaderBuf);
		Snmpv3BufferPut(0x01,&gSNMPv3PduHeaderBuf);
		retBuf = Snmpv3BufferPut(snmpEngineSecurityModel,&gSNMPv3PduHeaderBuf);
		if(retBuf != TRUE)
			return SNMP_NO_CREATION;
	}
	return SNMP_NO_ERR;
}






void Snmpv3UsmAuthoritativeEngnKeyLocalization(void)
{
static HASH_SUM md5;
UINT8 *cp, password_buf[64];
UINT32 password_index = 0;
UINT32 count = 0, i;
UINT8 localizedAuthKey[16];
	
	MD5Initialize(&md5);

	while (count < 1048576)
	{
		cp = password_buf;
		for (i = 0; i < 64; i++) 
		{
			*cp++ = snmpInMsgAuthParamStrng[password_index++ % 8];
		}


		MD5AddData(&md5, password_buf, 64);
		count+=64;
	}
	MD5Calculate(&md5, localizedAuthKey);
	memcpy(password_buf, localizedAuthKey, 16);
	memcpy(password_buf+16, snmpEngineID, snmpEngnIDLength);
	memcpy(password_buf+16+snmpEngnIDLength, localizedAuthKey, 16);

	MD5Initialize(&md5);
	MD5AddData(&md5,password_buf,32+snmpEngnIDLength);
		
	MD5Calculate(&md5, localizedAuthKey);
	count+=64;
	return;
}



/****************************************************************************
  Function: 
  	SNMP_ACTION Snmpv3UserSecurityModelProcessPDU(BYTE inOutPdu)

  Summary:
  	This routine collects or populates the security model parametrs infomation 
  	from the received SNMPv3 request PDU or to the response PDU respectively.
  
  Description:
	The recievd SNMPv3 PDU or the transmit PDU header has message security
	data bytes infomration. This routine retrievs the messgae security parameters
	infomration from the stored incoming pdu or write the appropriate security
	model info to the repsonse msg buffer.
		  	 		 		  	
  Precondition:
	Valid SNMPv3 request msg is received.
   	
  Parameters:
  	inOutPdu: indicates whether the incomig PDU is to be read for user security
  	model to be retrieved or the response PDU to be populated with these values 
  	
  Return Values:
	SNMP_NO_CREATION: Failure due to improper security model processing information 
					     format in the received PDU or failure in constructing the response PDU.
	SNMP_NO_ERR: The user security model retrieval or response PDU fomration is successful
				   
  Remarks:
  	The user security parameter constitute the vital information for the message  
	authentication and privacy of the message.
  	The user security model parameters header structure
	MsgAuthEngnID+MsgAuthEngnBoots+MsgAuthEngnTime
	+MsgUserName+MsgAuthParam+MsgPrivParam
***************************************************************************/
SNMP_ACTION Snmpv3UserSecurityModelProcessPDU(BYTE inOutPdu)
{
	DWORD_VAL tempLen={0};
	BYTE* ptr=NULL;	
	BYTE engnIdCntr=0;	
	BYTE tempData=0,putCntr=0;
	UINT16 tempPos;

	tempPos=snmpMsgBufSeekPos;

	if(inOutPdu == SNMP_REQUEST_PDU)
	{
	
		tempData = Snmpv3GetWholeMsgBufferData(gSnmpV3InPduWholeMsgBuf.snmpMsgHead,&tempPos);
		 if ( !IS_OCTET_STRING(tempData) )
		    return SNMP_NO_CREATION;
		 
		//Msg security Parameter length
		tempLen.Val=Snmpv3GetWholeMsgBufferData(gSnmpV3InPduWholeMsgBuf.snmpMsgHead,&tempPos);	
			
		 //Start collecting the security parameters from the incoming PDU.
		 //Check if the security parametrs are binded in ASN structure format 
		if (!_IsSNMPv3ValidStructure(gSnmpV3InPduWholeMsgBuf.snmpMsgHead,&tempPos,(WORD*)&tempLen.w[0]))
			return SNMP_NO_CREATION;

		 //Collect "msgAuthoritiveEngineID" 
		tempData=Snmpv3GetWholeMsgBufferData(gSnmpV3InPduWholeMsgBuf.snmpMsgHead,&tempPos);	
		 if ( !IS_OCTET_STRING(tempData) )
		    return FALSE;
		 
		tempData=Snmpv3GetWholeMsgBufferData(gSnmpV3InPduWholeMsgBuf.snmpMsgHead,&tempPos);	

		securityPrimitivesOfIncomingPdu.securityEngineIDLen=tempData;
		if(tempData == 0x00)
		{
			securityPrimitivesOfIncomingPdu.securityEngineID = NULL;
		}
		else
		{
			securityPrimitivesOfIncomingPdu.securityEngineID=ptr=(BYTE *)malloc((size_t)tempData+5);
			if(securityPrimitivesOfIncomingPdu.securityEngineID == NULL)
				return SNMP_NO_CREATION;
			while( tempData--)
			{
		       *ptr++ = Snmpv3GetWholeMsgBufferData(gSnmpV3InPduWholeMsgBuf.snmpMsgHead,&tempPos);	
			}	
		}

		//Check and collect "msgAuthoritiveEngineBoots"	
		if(! _Snmpv3IsValidInt(gSnmpV3InPduWholeMsgBuf.snmpMsgHead,&tempPos,&tempLen.Val))
		return SNMP_NO_CREATION; 

		authoritativeSnmpEngineBoots.Val= tempLen.Val;

		//Check and collect "msgAuthoritiveEngineTime"	
			 if(! _Snmpv3IsValidInt(gSnmpV3InPduWholeMsgBuf.snmpMsgHead,&tempPos,&tempLen.Val))
			return SNMP_NO_CREATION;	
		 
		authoritativeSnmpEngineTime.Val= tempLen.Val;


		//Collect "msgUserName"	
		tempData = Snmpv3GetWholeMsgBufferData(gSnmpV3InPduWholeMsgBuf.snmpMsgHead,&tempPos);	
		 if ( !IS_OCTET_STRING(tempData) )
		    return FALSE;
		 
		tempData = Snmpv3GetWholeMsgBufferData(gSnmpV3InPduWholeMsgBuf.snmpMsgHead,&tempPos);	
		securityPrimitivesOfIncomingPdu.securityNameLength=tempData;

		if(tempData == 0x00)
		{
			securityPrimitivesOfIncomingPdu.securityName = NULL;
		}
		else
		{
			securityPrimitivesOfIncomingPdu.securityName=ptr=(BYTE *)malloc((size_t)tempData+5);
			if(securityPrimitivesOfIncomingPdu.securityName == NULL)
				return SNMP_NO_CREATION;
			while( tempData--)
			{
			   *ptr++ = Snmpv3GetWholeMsgBufferData(gSnmpV3InPduWholeMsgBuf.snmpMsgHead,&tempPos);	
			}	
		
		}


		//validate user security name with security level
		if(!Snmpv3ValidateSecNameAndSecLvl())
			return SNMP_NO_CREATION;
		
		//Validate if the "msgAuthoritiveEngineID" matches to this agent's SNMP Engine ID
		if(!Snmpv3ValidateEngineId())
			return SNMP_NO_CREATION; 

		//Check and collect "msgAuthenticationParameters"	
		tempData = Snmpv3GetWholeMsgBufferData(gSnmpV3InPduWholeMsgBuf.snmpMsgHead,&tempPos);	
		 if ( !IS_OCTET_STRING(tempData) )
		    return FALSE;

		 //(snmpInMsgAuthParamLen should be 12 bytes if using HAMC-MD5-96 or HMAC-SHA-96)
		snmpInMsgAuthParamLen=tempData= Snmpv3GetWholeMsgBufferData(gSnmpV3InPduWholeMsgBuf.snmpMsgHead,&tempPos);	

		if((snmpSecurityLevel&0x01)==0x01)//If message is authenticated
		if(snmpInMsgAuthParamLen !=12 /* if using HAMC-MD5-96 or HMAC-SHA-96 */)
			return SNMP_NO_CREATION;
		
		if(tempData != 0x00)
		{
			ptr=snmpInMsgAuthParamStrng;
			
			gSnmpV3InPduWholeMsgBuf.msgAuthParamOffsetInWholeMsg=tempPos;//From snmpMsgHead;
			while( tempData--)
			{
			   *ptr++= Snmpv3GetWholeMsgBufferData(gSnmpV3InPduWholeMsgBuf.snmpMsgHead,&tempPos);	
			   
			}	
		}

		
		//Check and collect "msgPrivacyParameters"	
		tempData = Snmpv3GetWholeMsgBufferData(gSnmpV3InPduWholeMsgBuf.snmpMsgHead,&tempPos);	
		 if ( !IS_OCTET_STRING(tempData) )
		    return FALSE;

		//(snmpInMsgPrivParamLen should be 8 bytes) 
		snmpInMsgPrivParamLen=tempData =Snmpv3GetWholeMsgBufferData(gSnmpV3InPduWholeMsgBuf.snmpMsgHead,&tempPos);	
		if((snmpSecurityLevel&0x02)==0x02)//If message is encrypted
		if(snmpInMsgPrivParamLen !=8)
			return SNMP_NO_CREATION;
		
		if(tempData != 0x00)
		{
			ptr=snmpInMsgPrvParamStrng;
			
			while( tempData--)
			{
			   *ptr++ = Snmpv3GetWholeMsgBufferData(gSnmpV3InPduWholeMsgBuf.snmpMsgHead,&tempPos);	
			}	


			//This is a secured request. Compute the AES decryption IV 
			Snmpv3UsmAesEncryptDecryptInitVector(SNMP_REQUEST_PDU);
		}

		/* global variable to find out how many times SNMPv3 engine id has been validated*/
		gUsmStatsEngineID.Val++;
		snmpMsgBufSeekPos=tempPos;
		
	}
	else if(inOutPdu == SNMP_RESPONSE_PDU)
	{
		UINT16 snmpv3MsgAuthHeaderLength=0;
		BOOL   retBuf=TRUE;
		UINT16 msgHeaderOffset1=0;
		UINT16 msgHeaderOffset2=0;
		UINT16 tempMsgHeaderOffset=0;
		
		Snmpv3BufferPut(OCTET_STRING,&gSNMPv3PduHeaderBuf);  //Security Parameter string 	
		msgHeaderOffset1 = gSNMPv3PduHeaderBuf.length;
		Snmpv3BufferPut(MSG_AUTHORITATIVE_HEADER_LEN(snmpv3MsgAuthHeaderLength)-2,&gSNMPv3PduHeaderBuf);
		Snmpv3BufferPut(STRUCTURE,&gSNMPv3PduHeaderBuf);
		msgHeaderOffset2 = gSNMPv3PduHeaderBuf.length;
		Snmpv3BufferPut(MSG_AUTHORITATIVE_HEADER_LEN(snmpv3MsgAuthHeaderLength)-4,&gSNMPv3PduHeaderBuf);
		
		//Put "msgAuthoritiveEngineID"	
		Snmpv3BufferPut(OCTET_STRING,&gSNMPv3PduHeaderBuf);	
		Snmpv3BufferPut(snmpEngnIDLength,&gSNMPv3PduHeaderBuf); //Integer Length
		tempData=snmpEngnIDLength;
		for(;engnIdCntr<tempData;engnIdCntr++)
		{
			Snmpv3BufferPut(snmpEngineID[engnIdCntr],&gSNMPv3PduHeaderBuf);
		}
		
		//Put "msgAuthoritiveEngineBoots" 
		Snmpv3BufferPut(ASN_INT,&gSNMPv3PduHeaderBuf);	
		Snmpv3BufferPut(0x04,&gSNMPv3PduHeaderBuf);
		Snmpv3BufferPut(snmpEngineBoots>>24,&gSNMPv3PduHeaderBuf);
		Snmpv3BufferPut(snmpEngineBoots>>16,&gSNMPv3PduHeaderBuf);
		Snmpv3BufferPut(snmpEngineBoots>>8,&gSNMPv3PduHeaderBuf);
		Snmpv3BufferPut(snmpEngineBoots,&gSNMPv3PduHeaderBuf);

		//Put "msgAuthoritiveEngineTime" 
		Snmpv3GetAuthEngineTime();
		Snmpv3BufferPut(ASN_INT,&gSNMPv3PduHeaderBuf);	
		Snmpv3BufferPut(0x04,&gSNMPv3PduHeaderBuf); 
		Snmpv3BufferPut(snmpEngineTime.v[3],&gSNMPv3PduHeaderBuf);
		Snmpv3BufferPut(snmpEngineTime.v[2],&gSNMPv3PduHeaderBuf);
		Snmpv3BufferPut(snmpEngineTime.v[1],&gSNMPv3PduHeaderBuf);
		Snmpv3BufferPut(snmpEngineTime.v[0],&gSNMPv3PduHeaderBuf);


		//Put "msgUserName"	
		Snmpv3BufferPut(OCTET_STRING,&gSNMPv3PduHeaderBuf);	
		Snmpv3BufferPut(securityPrimitivesOfIncomingPdu.securityNameLength,&gSNMPv3PduHeaderBuf);
		tempData=securityPrimitivesOfIncomingPdu.securityNameLength ;
		if(securityPrimitivesOfIncomingPdu.securityNameLength != 0)
		{
			ptr= securityPrimitivesOfIncomingPdu.securityName;
			for(putCntr=0;putCntr<tempData;putCntr++)
			{
				//Snmpv3BufferPut(ptr[putCntr],&gSNMPv3PduHeaderBuf);
				Snmpv3BufferPut(*(ptr+putCntr),&gSNMPv3PduHeaderBuf);
			}
		}

		putCntr = 0;
		
		//Snmpv3UsmOutMsgAuthenticationParam(SNMPV3_HAMC_MD5/*Hash Accoding to user*/);
		//Put "msgAuthenticationParameters"	
		Snmpv3BufferPut(OCTET_STRING,&gSNMPv3PduHeaderBuf);
		if((snmpSecurityLevel & 0x01) == 0x01)
		{
			Snmpv3BufferPut(snmpOutMsgAuthParamLen,&gSNMPv3PduHeaderBuf); //Not supported with the Alpha Release.

			gSNMPv3PduHeaderBuf.msgAuthParamOffset=gSNMPv3PduHeaderBuf.length;

			//Put 0x00 to msgAuthenticationParameters, Once the response WholeMsg is 
			//populated, this offset can be updated with the new msgAuthenticationParam
			for(;putCntr<snmpOutMsgAuthParamLen;putCntr++)
			Snmpv3BufferPut(0x00,&gSNMPv3PduHeaderBuf);//RFC3414 Section 6.3.2 Page#56 Step3
		}
		else
		{
			Snmpv3BufferPut(0x00,&gSNMPv3PduHeaderBuf); //Not supported with the Alpha Release.
		}
		putCntr = 0;
		Snmpv3USMOutMsgPrivParam();
		
		//Put "msgPrivacyParameters" 
		Snmpv3BufferPut(OCTET_STRING,&gSNMPv3PduHeaderBuf); 
		if((snmpSecurityLevel & 0x02) == 0x02)
		{
			Snmpv3BufferPut(snmpOutMsgPrivParamLen,&gSNMPv3PduHeaderBuf); //Not supported with the Alpha Release
			for(;putCntr<snmpOutMsgPrivParamLen;putCntr++)
				retBuf = Snmpv3BufferPut(snmpOutMsgPrvParamStrng[putCntr],&gSNMPv3PduHeaderBuf);
		}
		else
		{
			Snmpv3BufferPut(0x00,&gSNMPv3PduHeaderBuf); //Not supported with the Alpha Release.
		}
		if(retBuf != TRUE)
			return SNMP_NO_CREATION;
		tempMsgHeaderOffset = gSNMPv3PduHeaderBuf.length;
		gSNMPv3PduHeaderBuf.length = msgHeaderOffset2;
		Snmpv3BufferPut((tempMsgHeaderOffset-msgHeaderOffset2)-1,&gSNMPv3PduHeaderBuf); 
		gSNMPv3PduHeaderBuf.length = tempMsgHeaderOffset;

		tempMsgHeaderOffset = gSNMPv3PduHeaderBuf.length;
		gSNMPv3PduHeaderBuf.length = msgHeaderOffset1;
		Snmpv3BufferPut((tempMsgHeaderOffset-msgHeaderOffset1)-1,&gSNMPv3PduHeaderBuf);
		gSNMPv3PduHeaderBuf.length = tempMsgHeaderOffset;
	}
	return SNMP_NO_ERR;
}


/****************************************************************************
  Function: 
  	SNMP_ACTION Snmpv3ScopedPduProcessing(BYTE inOutPdu)

  Summary:
  	This routine collects  the scoped pdu header information from the 
  	received SNMPv3 request PDU or populates to the response PDU respectively.
  
  Description:
	The recievd SNMPv3 PDU or the transmit PDU header has scoped pdu parameters
	like 'contextEngineID' 'context name' etc. This routine retrievs these parameters
	infomration from the stored incoming pdu or write the appropriate dynamically 
	allocated memory for the transmit response PDU.
		  	 		 		  	
  Precondition:
	Valid SNMPv3 request msg is received.
   	
  Parameters:
  	inOutPdu: indicates whether the incomig PDU is to be read for scoped pdu
  	paraemters to be retrieved or the response PDU to be populated with these values 
  	
  Return Values:
	SNMP_NO_CREATION: Failure due to improper scoped pdu information format in the  
					     PDU or failure in constructing the response PDU.
	SNMP_NO_ERR: The scoped parameters retrieval or response PDU fomration 
				   is successful
				   
  Remarks:
  	The scoped pDu parameters 
	msg data : - <contextEngineID><context name>[<data> == <pdutype><request id>
	<error status><error index><varbinds>
***************************************************************************/
SNMP_ACTION Snmpv3ScopedPduProcessing(BYTE inOutPdu)
{
	DWORD_VAL tempLen={0};
	UINT8* ptr=NULL;
	WORD msgDataLen=0;
	SNMPV3MSGDATA scopedPtr={NULL,0,0,0};

	UINT16 	contextIDlen=0;
	UINT16	contextNameLength=0;
	UINT16	snmpv3Headerlength=0,snmpv3MsgGlobalHeaderlength=0;
	UINT16	snmpv3MsgAuthHedaerLength=0;

	if(inOutPdu == SNMP_REQUEST_PDU)
	{
		if ( !_Snmpv3IsValidAuthStructure((WORD*)&tempLen) )
		{
			return SNMP_NO_CREATION;
		}

		gSnmpV3InPduWholeMsgBuf.scopedPduOffset=snmpMsgBufSeekPos;
		

		gSNMPv3ScopedPduRequestBuf.head=gSnmpV3InPduWholeMsgBuf.snmpMsgHead+snmpMsgBufSeekPos;
		gSNMPv3ScopedPduRequestBuf.length = 0;
		gSNMPv3ScopedPduRequestBuf.maxlength = tempLen.Val+1;
	}
	else if(inOutPdu == SNMP_RESPONSE_PDU)
	{		
			
		snmpv3Headerlength = MSGGLOBAL_HEADER_LEN(snmpv3MsgGlobalHeaderlength)+
									  MSG_AUTHORITATIVE_HEADER_LEN(snmpv3MsgAuthHedaerLength);
		
		msgDataLen = SNMP_MAX_MSG_SIZE - snmpv3Headerlength;
		ptr = gSNMPv3ScopedPduResponseBuf.head =(UINT8*)(malloc((size_t)msgDataLen+5));
		if(ptr == NULL)
		{
			return SNMP_NO_CREATION;
		}
		gSNMPv3ScopedPduResponseBuf.length = 0;
		gSNMPv3ScopedPduResponseBuf.maxlength = msgDataLen;
		gSNMPv3ScopedPduDataPos = 0;


    	//Start collecting the plaint text Scoped PDU data byte from the WholeMsg buffer
		//Check if the plain text scoped pdu data bytes are binded in ASN structure format 
		scopedPtr = gSNMPv3ScopedPduResponseBuf;
		Snmpv3BufferPut(STRUCTURE,&scopedPtr); // First item to Response buffer is packet structure
		Snmpv3BufferPut(0x82,&scopedPtr); 
		Snmpv3BufferPut(0,&scopedPtr);
		Snmpv3BufferPut(0,&scopedPtr);

		if((snmpSecurityLevel & 0x02)==0x02)
		{
			contextIDlen=Snmpv3GetBufferData(gSNMPv3ScopedPduRequestBuf,gSNMPv3ScopedPduDataPos++) ;
			contextIDlen=Snmpv3GetBufferData(gSNMPv3ScopedPduRequestBuf,gSNMPv3ScopedPduDataPos++) ;
			if(contextIDlen == 0x81)
			{
				Snmpv3GetBufferData(gSNMPv3ScopedPduRequestBuf,gSNMPv3ScopedPduDataPos++) ;
			}
			else if(contextIDlen == 0x82)
			{
				Snmpv3GetBufferData(gSNMPv3ScopedPduRequestBuf,gSNMPv3ScopedPduDataPos++) ;
				Snmpv3GetBufferData(gSNMPv3ScopedPduRequestBuf,gSNMPv3ScopedPduDataPos++) ;
			}
		}
		
		//Collect context engine id
		if (!IS_OCTET_STRING(Snmpv3GetBufferData(gSNMPv3ScopedPduRequestBuf,gSNMPv3ScopedPduDataPos) ))
		{
			return SNMP_NO_CREATION;
		}
		Snmpv3BufferPut(OCTET_STRING,&scopedPtr);

		contextIDlen = Snmpv3GetBufferData(gSNMPv3ScopedPduRequestBuf,++gSNMPv3ScopedPduDataPos);
		if(contextIDlen == 0)
		{			
			Snmpv3BufferPut(0,&scopedPtr);
		}
		else
		{
			//copy context engine id from a local buffer			
			Snmpv3BufferPut(contextIDlen,&scopedPtr);
			while(contextIDlen!=0)	
			{
				Snmpv3BufferPut(Snmpv3GetBufferData(gSNMPv3ScopedPduRequestBuf,++gSNMPv3ScopedPduDataPos),&scopedPtr);
				contextIDlen-=1;
			}
		}

		//Check and collect "contextName" 
		 if (!IS_OCTET_STRING(Snmpv3GetBufferData(gSNMPv3ScopedPduRequestBuf,++gSNMPv3ScopedPduDataPos) ))
		{
		   return SNMP_NO_CREATION;
		}
		Snmpv3BufferPut(OCTET_STRING,&scopedPtr);
		contextNameLength = (UINT16)Snmpv3GetBufferData(gSNMPv3ScopedPduRequestBuf,++gSNMPv3ScopedPduDataPos);
		if(contextNameLength == 0x00)
		{
			Snmpv3BufferPut(0x00,&scopedPtr);
		}
		else
		{
			Snmpv3BufferPut(contextNameLength,&scopedPtr);
			while(contextNameLength!=0x00)
			{
				Snmpv3BufferPut(Snmpv3GetBufferData(gSNMPv3ScopedPduRequestBuf,++gSNMPv3ScopedPduDataPos),&scopedPtr);
				contextNameLength-=1;
			}	
		}

		gSNMPv3ScopedPduResponseBuf.length = scopedPtr.length;

	}
	
	return SNMP_NO_ERR;
}



/****************************************************************************
  Function:
	void Snmpv3FreeDynAllocMem(void)
	
  Summary:
  	Allocated dynamic memory freeing is done by this routine.
	
  Description:
  	On the successful completion of the processing of the SNMPv3 request, or the 
  	failure in the processing due to improper PDU formats, the allocated dynamic
  	memory is required to be freed. This routine calls the free(), to deallocate memory.
	
  Precondition:
	The dyanmic memory buffer is allocated.
	
  Parameters:
  	None
  	
  Return Values:
	None
	
  Remarks:
	The SNMPv3 stack does uses the dynamic memory extensively for different 
       processing needs, hence incoming and outgoing pdu memory buffers are created.
	This routine checks for the memory is being allocated before it attempts for the deallocation. 
 ***************************************************************************/
void Snmpv3FreeDynAllocMem(void)
{

	if(gSNMPv3PduHeaderBuf.head != NULL)
	{
		free(gSNMPv3PduHeaderBuf.head);
		gSNMPv3PduHeaderBuf.head=NULL;
		gSNMPv3PduHeaderBuf.length=0x00;
	}

	if(gSNMPv3ScopedPduResponseBuf.head != NULL)
	{
		free(gSNMPv3ScopedPduResponseBuf.head);
		gSNMPv3ScopedPduResponseBuf.head=NULL;
		gSNMPv3ScopedPduResponseBuf.length = 0;
	}

	if(gSnmpV3InPduWholeMsgBuf.wholeMsgHead != NULL)
	{
		free(gSnmpV3InPduWholeMsgBuf.wholeMsgHead);
		gSnmpV3InPduWholeMsgBuf.wholeMsgLen.Val = 0;
		gSnmpV3InPduWholeMsgBuf.wholeMsgHead=NULL;
		gSnmpV3InPduWholeMsgBuf.snmpMsgHead=NULL;
	}

	if(securityPrimitivesOfIncomingPdu.securityEngineID!=NULL)
	{
		free(securityPrimitivesOfIncomingPdu.securityEngineID);
		securityPrimitivesOfIncomingPdu.securityEngineID=0x00;
		securityPrimitivesOfIncomingPdu.securityEngineIDLen=0x00;
	}

	if(securityPrimitivesOfIncomingPdu.securityName != NULL)
	{ 
		free(securityPrimitivesOfIncomingPdu.securityName);
		securityPrimitivesOfIncomingPdu.securityName=NULL;
	}

	if(gSNMPv3TrapMsgHeaderBuf.head != NULL)
	{
		free(gSNMPv3TrapMsgHeaderBuf.head);
		gSNMPv3TrapMsgHeaderBuf.length=0;
        gSNMPv3TrapMsgHeaderBuf.head = NULL;
	}

	if(gSNMPv3TrapScopedPduResponseBuf.head != NULL)
	{
		free(gSNMPv3TrapScopedPduResponseBuf.head);
		gSNMPv3TrapScopedPduResponseBuf.length = 0;
		gSNMPv3TrapScopedPduResponseBuf.head = NULL;
	}
}

/****************************************************************************
  Function:
	BOOL ProcessSnmpv3MsgData(PDU_INFO* pduDbPtr)
	
  Summary:
  	This routine processes the snmpv3 request and parallely creates the response pdu.
	
  Description:
  	Once the received pdu is validated as Snmpv3 pdu, it is forwarded for 
  	processing to this routine. This rotuine handles Get, Get_Next, Get_Bulk,
  	Set request and creates appropriate response as Get_Response. 
  	This routine will decide on whether the request pdu should be processed
  	or be discarded. 
  	
  Precondition:
	The received udp packet is varified as valid SNMPv3 request.
		
  Parameters:
  	pduDbPtr  - Pointer to received pdu information database
  	
  Return Values:
	TRUE 	- If the snmp request processing is successful.
	FALSE	- If the processing failed else the processing is not completed.
	
  Remarks:
	None
 ***************************************************************************/
BOOL ProcessSnmpv3MsgData(PDU_INFO* pduDbPtr)
{
	BYTE 			Getbulk_N=0,Getbulk_M=0,Getbulk_R=0;/*Refer RFC 3416 Section "4.2.3" GetBulkRequest-PDU*/
	BYTE			OIDValue[OID_MAX_LEN];
	BYTE			OIDlen=0;
	BYTE			oidLookUpRet=0;
	UINT8			noOfVarbindreq=0xFF;
	UINT8 tempBuf[4];
	UINT8 tempCntr=0;
	UINT8* tempPtr=NULL;
	UINT8* outBufPtr=NULL;
	BYTE			varIndex=0;
	BYTE 			repeatCntr=0,varBindCntr=0;
	BYTE			succesor=0,tempRet=0xFF;
	UINT16	 		pduLenOffset=0;
	UINT16 	 		pduLength=0;
	WORD 			errorStatusOffset=0;
	WORD 			errorIndexOffset=0;
	WORD 			varBindHeaderLen=0;
	WORD			previousGetBufpos=0;
	WORD			varBindHeaderOffset=0;
	WORD			varBindHeaderOffset_2=0;
	WORD			varBindHeaderOffset_3=0;
	WORD			contextNameOffset=0;	
	WORD		 	varStructLenOffset=0;
	WORD			maxRepeatationOffset=0;
	WORD			tempOffset=0;						
	WORD_VAL		varPairLen = {0x0};
	DWORD_VAL 		tempVal={0};
	static SNMPV3MSGDATA	*dynScopedBufPtr=NULL;
	OID_INFO		OIDInfo;  
	SNMP_ERR_STATUS errorStatus;

		
	enum 
	{
		SM_PKT_STRUCT_LEN_OFFSET=0u,
		SM_RESPONSE_PDU_LEN_OFFSET,
		SM_ERROR_STATUS_OFFSET,
		SM_ERROR_INDEX_OFFSET,
		SM_FIND_NO_OF_REQUESTED_VARBINDS,
		SM_FIND_NO_OF_RESPONSE_VARBINDS,
		SM_VARBIND_STRUCT_OFFSET,
		SM_VARSTRUCT_LEN_OFFSET,
		SM_POPULATE_REQ_OID,
		SM_FIND_OID_IN_MIB,
		SM_NON_REPETITIONS,
		SM_MAX_REPETITIONS
	}smSnmp=SM_PKT_STRUCT_LEN_OFFSET;

	dynScopedBufPtr = &gSNMPv3ScopedPduResponseBuf;
	
	while(1)
	{
		switch(smSnmp)
		{
	
			// Before each variables are processed, prepare necessary header.
				case SM_PKT_STRUCT_LEN_OFFSET:
	
				varPairLen.Val=0x0000;
				
				if(Snmpv3MsgProcessingModelProcessPDU(SNMP_RESPONSE_PDU)!= SNMP_NO_ERR)
				{
					Snmpv3FreeDynAllocMem();
					return FALSE;
				}
				if(Snmpv3UserSecurityModelProcessPDU(SNMP_RESPONSE_PDU)!= SNMP_NO_ERR)
				{
					Snmpv3FreeDynAllocMem();
					return FALSE;
				}
				contextNameOffset = dynScopedBufPtr->length;
				if(Snmpv3ScopedPduProcessing(SNMP_RESPONSE_PDU)!= SNMP_NO_ERR)
				{
					Snmpv3FreeDynAllocMem();
					return FALSE;
				}
				
				dynScopedBufPtr = &gSNMPv3ScopedPduResponseBuf;					
				dynScopedBufPtr->head = gSNMPv3ScopedPduResponseBuf.head;
				dynScopedBufPtr->length = gSNMPv3ScopedPduResponseBuf.length;
				
				pduDbPtr->pduType = Snmpv3GetBufferData(gSNMPv3ScopedPduRequestBuf,++gSNMPv3ScopedPduDataPos);
				pduLength = Snmpv3GetBufferData(gSNMPv3ScopedPduRequestBuf,++gSNMPv3ScopedPduDataPos);
				if(pduLength == 0x81)
				{
					pduLength = Snmpv3GetBufferData(gSNMPv3ScopedPduRequestBuf,++gSNMPv3ScopedPduDataPos);
				}
				else if(pduLength == 0x82)
				{
					pduLength = Snmpv3GetBufferData(gSNMPv3ScopedPduRequestBuf,++gSNMPv3ScopedPduDataPos);
					pduLength = Snmpv3GetBufferData(gSNMPv3ScopedPduRequestBuf,++gSNMPv3ScopedPduDataPos);
				}					
			
				varBindHeaderOffset = dynScopedBufPtr->length;
				previousGetBufpos = gSNMPv3ScopedPduDataPos;
				if(Snmpv3GetBufferData(gSNMPv3ScopedPduRequestBuf,previousGetBufpos+0x0E)==0x0)
				{
					noOfVarbindreq = 0;
				}
				smSnmp++;
			case SM_RESPONSE_PDU_LEN_OFFSET:

				if(!noOfVarbindreq)
					Snmpv3BufferPut(REPORT_RESPONSE,dynScopedBufPtr);
				else
					Snmpv3BufferPut(GET_RESPONSE,dynScopedBufPtr);			
				// Since we don't know length of this response, use placeholders until
				pduLenOffset = dynScopedBufPtr->length;
				Snmpv3BufferPut(0x82,dynScopedBufPtr);				
				Snmpv3BufferPut(0,dynScopedBufPtr);
				Snmpv3BufferPut(0,dynScopedBufPtr);
				
				if(Snmpv3IsValidInt(&tempVal.Val) != TRUE)
				{					
					Snmpv3FreeDynAllocMem();
					return FALSE;
				}
				else
				{
					// Put original request back.
					Snmpv3BufferPut(ASN_INT,dynScopedBufPtr);	// Int type.
					Snmpv3BufferPut(4,dynScopedBufPtr);		// To simplify logic, always use 4 byte long requestID
					Snmpv3BufferPut(tempVal.v[3],dynScopedBufPtr); // Start MSB
					Snmpv3BufferPut(tempVal.v[2],dynScopedBufPtr);
					Snmpv3BufferPut(tempVal.v[1],dynScopedBufPtr);
					Snmpv3BufferPut(tempVal.v[0],dynScopedBufPtr);
				}

				smSnmp++;
			case SM_ERROR_STATUS_OFFSET :
				/*update pduDbPtr structure for error index and eroor status 
				and non repeators and max repeators */
				if(pduDbPtr->pduType != GET_BULK_REQUEST)
				{
					// ignore error index and error status but update pduDBptr
					tempVal.Val = 0;
					Snmpv3IsValidInt(&tempVal.Val);
					pduDbPtr->errorStatus = tempVal.Val;
					tempVal.Val = 0;
					Snmpv3IsValidInt(&tempVal.Val);
					pduDbPtr->erroIndex = tempVal.Val;
				}
				else
				{
					// update max repeators and non repeators
					tempVal.Val = 0;
					if(Snmpv3IsValidInt(&tempVal.Val) == TRUE)
						pduDbPtr->nonRepeators = tempVal.Val;
					else
					{						
						Snmpv3FreeDynAllocMem();
						return FALSE;
					}
					tempVal.Val = 0;
					if(Snmpv3IsValidInt(&tempVal.Val) == TRUE)
						pduDbPtr->maxRepetitions = tempVal.Val;
					else
					{						
						Snmpv3FreeDynAllocMem();
						return FALSE;
					}
					
				}
				
				// Put error status.
				// Since we do not know error status, put place holder until we know it...
				Snmpv3BufferPut(ASN_INT,dynScopedBufPtr);				// Int type
				Snmpv3BufferPut(1,dynScopedBufPtr);					// One byte long.
				errorStatusOffset = dynScopedBufPtr->length;
				Snmpv3BufferPut(0,dynScopedBufPtr);					// Placeholder.
				smSnmp++;
	
			case SM_ERROR_INDEX_OFFSET :
	
				// Similarly put error index.
				Snmpv3BufferPut(ASN_INT,dynScopedBufPtr);				// Int type
				Snmpv3BufferPut(1,dynScopedBufPtr);					// One byte long
				errorIndexOffset = dynScopedBufPtr->length;
				Snmpv3BufferPut(0,dynScopedBufPtr);					// Placeholder.
	
				smSnmp++;
	
			case SM_FIND_NO_OF_REQUESTED_VARBINDS:

				varBindHeaderOffset_2 = dynScopedBufPtr->length;
				// Decode variable binding structure
				if ( IsSNMPv3ValidStructure(&varBindHeaderLen) == FALSE)
				{
					noOfVarbindreq = 0;						
				}
				else	//Find number of OIDs/varbinds's data requested in received PDU.
					noOfVarbindreq = FindOIDsFromSnmpV3Request(varBindHeaderLen);
				
				Snmpv3BufferPut(STRUCTURE,dynScopedBufPtr);
				varBindHeaderOffset_3 = dynScopedBufPtr->length;
				Snmpv3BufferPut(0x82,dynScopedBufPtr);
				Snmpv3BufferPut(0,dynScopedBufPtr);				
				Snmpv3BufferPut(0,dynScopedBufPtr);
				if(noOfVarbindreq == 0)
				{
					Snmpv3ReportPdu(dynScopedBufPtr);
					break;
				}
				smSnmp++;	
	
			case SM_FIND_NO_OF_RESPONSE_VARBINDS:
				//Calculate number of variables to be responded for the received request
				Getbulk_N = noOfVarbindreq; Getbulk_M=0; Getbulk_R=0;
				if((pduDbPtr->snmpVersion == (BYTE)SNMP_V3) && 
					(pduDbPtr->pduType == GET_BULK_REQUEST))
				{
					if((pduDbPtr->nonRepeators) <= noOfVarbindreq)
					{
						Getbulk_N = pduDbPtr->nonRepeators;
					}	
					Getbulk_M = pduDbPtr->maxRepetitions;
	
					if((noOfVarbindreq - Getbulk_N)>=0u)
						Getbulk_R = noOfVarbindreq-Getbulk_N;
					
					noOfVarbindreq = Getbulk_N + (Getbulk_M * Getbulk_R);//Refer RFC 3416 
					
					if(Getbulk_N == 0)
					{
						smSnmp=SM_MAX_REPETITIONS;
						break;
					}
				}	
				//noOfVarbindreq = Getbulk_N + (Getbulk_M * Getbulk_R);//Refer RFC 3416 
	
				smSnmp++;
			case SM_VARSTRUCT_LEN_OFFSET:
				if(noOfVarbindreq == 0)
					break;
				
				if(Getbulk_N!= 0u) // decreament non repeators.
					Getbulk_N--;
				else if(Getbulk_M > 0) // jump to max repeatations
				{
					smSnmp = SM_MAX_REPETITIONS;
					break;
				}
				
				varIndex++;
				if ( IsSNMPv3ValidStructure(&varBindHeaderLen) == FALSE)
				{
					Snmpv3SetErrorStatus(errorStatusOffset,errorIndexOffset,SNMP_GEN_ERR,varIndex,dynScopedBufPtr);
					goto SNMP_PROCESS_END;
				}
				smSnmp++;
			case SM_POPULATE_REQ_OID:
				for(OIDlen=0;OIDlen<sizeof(OIDValue);OIDlen++)
					OIDValue[OIDlen]=0;
				OIDlen=0;
				if(IsSnmpv3ValidOID(OIDValue,&OIDlen) == FALSE)
				{
					Snmpv3SetErrorStatus(errorStatusOffset,errorIndexOffset,SNMP_GEN_ERR,varIndex,dynScopedBufPtr);
					goto SNMP_PROCESS_END;
				}
				
				// For Get & Get-Next, value must be NULL.
				if ( pduDbPtr->pduType != (BYTE)SET_REQUEST )
				{
					if ( !IsSnmpV3ASNNull() )
					{						
						Snmpv3SetErrorStatus(errorStatusOffset,errorIndexOffset,SNMP_GEN_ERR,varIndex,dynScopedBufPtr);
						goto SNMP_PROCESS_END;
					}
				}
				noOfVarbindreq--;
				smSnmp++;
			
			case SM_FIND_OID_IN_MIB:
			
				/* Search for the requested OID in the MIB database with the agent.*/
				
				
				//Searching the requested OID in the MIB database 
				oidLookUpRet = OIDLookup(pduDbPtr,OIDValue, OIDlen, &OIDInfo);	
				if(Snmpv3BufferPut(STRUCTURE,dynScopedBufPtr) != TRUE)
					goto GET_BULK_OVERFLOW_ERROR;
				varStructLenOffset= dynScopedBufPtr->length;
				if(Snmpv3BufferPut(0,dynScopedBufPtr)!= TRUE)
					goto GET_BULK_OVERFLOW_ERROR;
		
				// ASN OID data type
				if(Snmpv3BufferPut(ASN_OID,dynScopedBufPtr)!= TRUE)
					goto GET_BULK_OVERFLOW_ERROR;
		
				/* send the error code for SNMPv3 version for GET request and SET - request.
				As the follwing code is only for the get and set response, so Snmpv3BufferPut is not
				under the buffer over flow check.
				*/
				if(oidLookUpRet != (BYTE)TRUE && (pduDbPtr->pduType != GET_NEXT_REQUEST) &&
					(pduDbPtr->pduType != GET_BULK_REQUEST))
				{
					if(appendZeroToOID)
						Snmpv3BufferPut(OIDlen+1,dynScopedBufPtr);//for appending "0"
					else 
						Snmpv3BufferPut(OIDlen,dynScopedBufPtr);//do not append "0"		
					pduLength = 0;							
					//Put OID
					while( OIDlen-- )
						Snmpv3BufferPut(OIDValue[pduLength++],dynScopedBufPtr);//do not append "0"		
					
					if(appendZeroToOID)
					{
						Snmpv3BufferPut(0x00,dynScopedBufPtr);//Appending '0' to OID in response
					}
					if(( pduDbPtr->snmpVersion == (BYTE)SNMP_V3)
							&& (pduDbPtr->pduType == SNMP_GET))
					{
						Snmpv3BufferPut(oidLookUpRet,dynScopedBufPtr);//Appending '0' to OID in response
						Snmpv3BufferPut(0x0,dynScopedBufPtr);//Appending '0' to OID in response
					}
					tempOffset = dynScopedBufPtr->length;
					pduLength = dynScopedBufPtr->length-(varStructLenOffset+1);
					dynScopedBufPtr->length = varStructLenOffset;
					Snmpv3BufferPut(pduLength,dynScopedBufPtr);
					dynScopedBufPtr->length = tempOffset;
					//Reset to state machine to access the next oid in request
					smSnmp=SM_VARSTRUCT_LEN_OFFSET;
					break;	
				}
				smSnmp++;
			
				//return FALSE;
				
				case SM_NON_REPETITIONS:
				
					/*	Variables in get,get_next,set and get_bulk ( non repetition variables)
						of snmp request are processed in this part of the state machine.*/

					if(pduDbPtr->pduType == SNMP_SET)
					{
						BYTE templen=OIDlen;
						BYTE *ptroid=OIDValue;	
						//to validate the REC ID is present or not
	
						if(SNMPIdRecrdValidation(pduDbPtr,&OIDInfo,OIDValue,OIDlen) != TRUE)
						{
							/*if(pduDbPtr->snmpVersion == (BYTE)SNMP_V1)
					       		*errorStatus = SNMP_NO_SUCH_NAME;
							else if ((pduDbPtr->snmpVersion == (BYTE)SNMP_V2C) ||
											(pduDbPtr->snmpVersion == (BYTE)SNMP_V3))*/

							 /*if the variable binding's name specifies a
						     * variable which does not exist and could not ever be
						     * created, then the value of the Response-PDU's error-
						     * status field is set to `noCreation', and the value of its
						     * error-index field is set to the index of the failed
						     * variable binding.
						     */
							errorStatus = SNMP_NO_CREATION;
							
							return FALSE;
						}
						
						if(appendZeroToOID)
							Snmpv3BufferPut(OIDlen+1,dynScopedBufPtr);//for appending "0"
						else 
							Snmpv3BufferPut(OIDlen,dynScopedBufPtr);//do not append "0"
						
						//Put OID
						while( templen-- )
							Snmpv3BufferPut(*ptroid++,dynScopedBufPtr);//do not append "0" 	
						
						if(appendZeroToOID)
						{
							Snmpv3BufferPut(0x00,dynScopedBufPtr);//Appending '0' to OID in response
						}
						//Now process the SET command
						tempRet = ProcessSetVar(pduDbPtr,&OIDInfo, &errorStatus);
				
						if ( errorStatus != SNMP_NO_ERR )
						{
							//SET var command failed. Update the error status.
							Snmpv3SetErrorStatus(errorStatusOffset, \
										   errorIndexOffset, \
										   errorStatus, \
										   varIndex,dynScopedBufPtr); \
				
						}	
						
					}/*Get-Next-rquest also calls the ProcessGetVar for 0the instance.  */
					else if((pduDbPtr->pduType == SNMP_GET) || (getZeroInstance) ||
						((pduDbPtr->pduType == SNMP_V2C_GET_BULK) && (oidLookUpRet == TRUE)))
					{	
						BYTE templen=OIDlen;
						BYTE *ptroid=OIDValue;	

						//to validate the REC ID is present or not
						if(SNMPIdRecrdValidation(pduDbPtr,&OIDInfo,OIDValue,OIDlen) != TRUE)
						{
							return FALSE;
						}
						if(appendZeroToOID)
						{
							if(Snmpv3BufferPut(OIDlen+1,dynScopedBufPtr)!= TRUE) //for appending "0"
								goto GET_BULK_OVERFLOW_ERROR;
						}
						else 
						{
							if(Snmpv3BufferPut(OIDlen,dynScopedBufPtr) != TRUE)//do not append "0"
								goto GET_BULK_OVERFLOW_ERROR;
						}
						
						//Put OID
						while( templen-- )
							if(Snmpv3BufferPut(*ptroid++,dynScopedBufPtr)!= TRUE)//do not append "0" 	
								goto GET_BULK_OVERFLOW_ERROR;
						
						if(appendZeroToOID)
						{
							if(Snmpv3BufferPut(0x00,dynScopedBufPtr)!= TRUE)//Appending '0' to OID in response
								goto GET_BULK_OVERFLOW_ERROR;
						}

						tempRet = ProcessGetVar(&OIDInfo,FALSE,pduDbPtr);				
					}	
					else if((pduDbPtr->pduType == SNMP_GET_NEXT)||
						((pduDbPtr->pduType == SNMP_V2C_GET_BULK) && (oidLookUpRet != TRUE)))
					{			
						tempRet = ProcessGetNextVar(&OIDInfo,pduDbPtr);
						if(tempRet ==0)
						{
							BYTE templen=OIDlen;
							BYTE *ptroid=OIDValue;	
							
							if(appendZeroToOID)
							{
								if(Snmpv3BufferPut(OIDlen+1,dynScopedBufPtr) != TRUE)//for appending "0"
									goto GET_BULK_OVERFLOW_ERROR;
							}
							else 
							{
								if(Snmpv3BufferPut(OIDlen,dynScopedBufPtr)!= TRUE)//do not append "0"
									goto GET_BULK_OVERFLOW_ERROR;
							}
							
							//Put OID
							while( templen-- )
								if(Snmpv3BufferPut(*ptroid++,dynScopedBufPtr)!= TRUE)//do not append "0" 
									goto GET_BULK_OVERFLOW_ERROR;
							
							if(appendZeroToOID)
							{
								if(Snmpv3BufferPut(0x00,dynScopedBufPtr)!= TRUE)//Appending '0' to OID in response
									goto GET_BULK_OVERFLOW_ERROR;
							}
						}
					}
				
				
					/*	If the request command processing is failed, update
						the error status, index accordingly and response pdu.*/ 
					if(tempRet == 0u &&(pduDbPtr->pduType != SNMP_SET))
					{
						if(dynScopedBufPtr->length >= dynScopedBufPtr->maxlength)
							goto GET_BULK_OVERFLOW_ERROR;
						if(((pduDbPtr->pduType == SNMP_GET_NEXT)|| (pduDbPtr->pduType == SNMP_V2C_GET_BULK))&&pduDbPtr->snmpVersion == (BYTE)SNMP_V3)
						{
							if(Snmpv3BufferPut(SNMP_END_OF_MIB_VIEW,dynScopedBufPtr)!= TRUE)
								goto GET_BULK_OVERFLOW_ERROR;
							if(Snmpv3BufferPut(0,dynScopedBufPtr)!= TRUE)
								goto GET_BULK_OVERFLOW_ERROR;
							//if get bulk response reaches END of mIB view break from the loop.
							noOfVarbindreq = 0;
							Getbulk_N = 0u; 					
						}
				
					}
					dynScopedBufPtr->length = gSNMPv3ScopedPduResponseBuf.length;
					tempOffset = dynScopedBufPtr->length;
					pduLength = dynScopedBufPtr->length-(varStructLenOffset+1);
					dynScopedBufPtr->length = varStructLenOffset;
					Snmpv3BufferPut(pduLength,dynScopedBufPtr);
					dynScopedBufPtr->length = tempOffset;

					/* to avoid Dynamic out buffer crash   we need to calculate buffer
					availability .Approximatly the next variable bind length should be less than 30.*/
					
					if(dynScopedBufPtr->length>= dynScopedBufPtr->maxlength)
					{
						noOfVarbindreq = 0;
						Getbulk_N = 0u;						
						break;
					}
					/*	Decide on the number of Non repetition variables remained to 
						be processed, decide the course of state machine.*/
					if((pduDbPtr->pduType==GET_BULK_REQUEST) && (pduDbPtr->snmpVersion == (BYTE)SNMP_V3)
														&&( Getbulk_N == 0u))
					{					
						smSnmp=SM_MAX_REPETITIONS;
					}
					else
						smSnmp=SM_VARSTRUCT_LEN_OFFSET;
				
					getZeroInstance = FALSE;
					break;
				case SM_MAX_REPETITIONS:
					maxRepeatationOffset = gSNMPv3ScopedPduDataPos;
					/*Process each variable in request as Get_Next for 
					  Getbulk_M (Max_repetition) times */
					for(repeatCntr=0;repeatCntr<Getbulk_M;repeatCntr++)
					{
						gSNMPv3ScopedPduDataPos = maxRepeatationOffset;
						
						//Process every veriable in the request.
						for(varBindCntr=0;varBindCntr<Getbulk_R;varBindCntr++)
						{
							if(noOfVarbindreq != 0)
							{
								noOfVarbindreq--;
							}
							else
								break;
							
							if(varBindCntr==0u)
								varIndex=(noOfVarbindreq - Getbulk_R);
				
							varIndex++;

							if(Snmpv3BufferPut(STRUCTURE,dynScopedBufPtr)!= TRUE)
								goto GET_BULK_OVERFLOW_ERROR;
							varStructLenOffset= dynScopedBufPtr->length;
							if(Snmpv3BufferPut(0,dynScopedBufPtr)!= TRUE)
								goto GET_BULK_OVERFLOW_ERROR;
							succesor=repeatCntr;
				
							// Decode variable length structure
							if(IsSNMPv3ValidStructure(&varBindHeaderLen) == FALSE)
							{
								Snmpv3SetErrorStatus(errorStatusOffset,errorIndexOffset,SNMP_GEN_ERR,varIndex,dynScopedBufPtr);
								goto SNMP_PROCESS_END;
								//return FALSE;
							}
				
							// Decode next object
							if ( !IsSnmpv3ValidOID(OIDValue, &OIDlen) )
							{
								Snmpv3SetErrorStatus(errorStatusOffset,errorIndexOffset,SNMP_GEN_ERR,varIndex,dynScopedBufPtr);
								goto SNMP_PROCESS_END;
								//return FALSE;
							}
							
							// For Get & Get-Next, value must be NULL.
							if ( pduDbPtr->pduType != (BYTE)SET_REQUEST )
								if ( !IsSnmpV3ASNNull() )
									break;
				
							oidLookUpRet = OIDLookup(pduDbPtr,OIDValue, OIDlen, &OIDInfo);
							if(oidLookUpRet == SNMP_END_OF_MIB_VIEW)
							{
								tempRet = GetNextLeaf(&OIDInfo);
							}
							if(oidLookUpRet == FALSE)
							{
								BYTE templen=OIDlen;
								BYTE *ptroid=OIDValue;	
								
								if(Snmpv3BufferPut(ASN_OID,dynScopedBufPtr)!= TRUE)
									goto GET_BULK_OVERFLOW_ERROR;
								if(appendZeroToOID)
								{
									if(Snmpv3BufferPut(OIDlen+1,dynScopedBufPtr)!= TRUE)
										goto GET_BULK_OVERFLOW_ERROR;
									//_SNMPPut(OIDLen+1);//for appending "0"
									OIDlen += 1;
								}
								else 
									if(Snmpv3BufferPut(OIDlen,dynScopedBufPtr) != TRUE)
										goto GET_BULK_OVERFLOW_ERROR;
				
								//Put OID
								while( templen-- )
									if(Snmpv3BufferPut(*ptroid++,dynScopedBufPtr) != TRUE)
										goto GET_BULK_OVERFLOW_ERROR;
								if(appendZeroToOID)
									if(Snmpv3BufferPut(0x0,dynScopedBufPtr) != TRUE)
										goto GET_BULK_OVERFLOW_ERROR;
								if(Snmpv3BufferPut(SNMP_END_OF_MIB_VIEW,dynScopedBufPtr) != TRUE)
									goto GET_BULK_OVERFLOW_ERROR;
								if(Snmpv3BufferPut(0x0,dynScopedBufPtr)!= TRUE)
									goto GET_BULK_OVERFLOW_ERROR;

								noOfVarbindreq = 0;

							}
							else if(tempRet != 0)//if(oidLookUpRet != SNMP_END_OF_MIB_VIEW)
							{
								tempRet = ProcessGetBulkVar(&OIDInfo, &OIDValue[0],&OIDlen,&succesor,pduDbPtr);
							}
							if ( tempRet == 0u )
							{
								BYTE templen=OIDlen;
								BYTE *ptroid=OIDValue;	
								if(Snmpv3BufferPut(ASN_OID,dynScopedBufPtr) != TRUE)
									goto GET_BULK_OVERFLOW_ERROR;
								if(appendZeroToOID)
								{
									if(Snmpv3BufferPut(OIDlen+1,dynScopedBufPtr)!= TRUE) //for appending "0"
										goto GET_BULK_OVERFLOW_ERROR;
									OIDlen += 1;
								}
								else 
									if(Snmpv3BufferPut(OIDlen,dynScopedBufPtr)!=  TRUE)
										goto GET_BULK_OVERFLOW_ERROR;
				
								//Put OID
								while( templen-- )
									if(Snmpv3BufferPut(*ptroid++,dynScopedBufPtr) != TRUE)
										goto GET_BULK_OVERFLOW_ERROR;
				
								/*Do send back the Same OID if get_next is EndOfMibView. Do not
								  append zero to this OID*/
								
								if(Snmpv3BufferPut(SNMP_END_OF_MIB_VIEW,dynScopedBufPtr) != TRUE)
									goto GET_BULK_OVERFLOW_ERROR;
								if(Snmpv3BufferPut(0x0,dynScopedBufPtr) != TRUE)
									goto GET_BULK_OVERFLOW_ERROR;
				
								//snmpReqVarErrStatus.endOfMibViewErr  |=(0x0001 << varIndex);
								if(appendZeroToOID)
									if(Snmpv3BufferPut(0x0,dynScopedBufPtr) != TRUE)
										goto GET_BULK_OVERFLOW_ERROR;

								noOfVarbindreq = 0;
								
							}
							
						
							dynScopedBufPtr = &gSNMPv3ScopedPduResponseBuf;
							tempOffset = dynScopedBufPtr->length;
							pduLength = dynScopedBufPtr->length -(varStructLenOffset+1);
							dynScopedBufPtr->length = varStructLenOffset;
							Snmpv3BufferPut(pduLength,dynScopedBufPtr);
							dynScopedBufPtr->length = tempOffset;

							/* if length dynamic buffer length increases more than the allocated memory 
							then break from the loop.*/
							if(dynScopedBufPtr->length>= dynScopedBufPtr->maxlength)
							{
								noOfVarbindreq = 0;
								Getbulk_N = 0u; 					
							    goto	GET_BULK_OVERFLOW_ERROR;
							}
							tempRet = 0xFF;
						}//for(varBindCntr=0;varBindCntr<Getbulk_R;varBindCntr++)						
					}//for(repeatCntr=0;repeatCntr<Getbulk_M;repeatCntr++)
					/* check length*/
				break;	

			default:				
				Snmpv3FreeDynAllocMem();
				return FALSE;
		}
		if(noOfVarbindreq == 0)
		{
			break;
		}
	}

GET_BULK_OVERFLOW_ERROR:
	if(dynScopedBufPtr->length >= dynScopedBufPtr->maxlength)
	{
		if(pduDbPtr->pduType == SNMP_V2C_GET_BULK)
		{
			pduLength = dynScopedBufPtr->length - (varStructLenOffset-1);
			dynScopedBufPtr->length = dynScopedBufPtr->length - pduLength;			
		}
		else
		{
			dynScopedBufPtr->length = varBindHeaderOffset_3;
			Snmpv3BufferPut(0,dynScopedBufPtr);
			Snmpv3SetErrorStatus(errorStatusOffset,errorIndexOffset,SNMP_TOO_BIG,varIndex,dynScopedBufPtr); 
		}
	}


SNMP_PROCESS_END:
	/* pass the data to wire*/
	{
		WORD	 	scopedpduHeaderOffset = 0;
		WORD_VAL 	totalPdulength = {0};
		WORD_VAL	scoped_pdu_len_1 = {0}; // context data length
		WORD_VAL	scoped_pdu_len_2 = {0}; // pdu response length
		WORD_VAL	scoped_pdu_len_3 = {0}; //variable binding header with varbinds
		WORD 		i=0;
		//DWORD       scopedPduHeadPtr=0;
		SNMPV3MSGDATA tempScopedData;
		
		scopedpduHeaderOffset = dynScopedBufPtr->length;
		tempScopedData = gSNMPv3ScopedPduResponseBuf;
		
		// update length for variable binds
		scoped_pdu_len_3.Val = (dynScopedBufPtr->length-3)-varBindHeaderOffset_3;
		dynScopedBufPtr->length = varBindHeaderOffset_3+1;
		Snmpv3BufferPut(scoped_pdu_len_3.v[1],dynScopedBufPtr);
		Snmpv3BufferPut(scoped_pdu_len_3.v[0],dynScopedBufPtr);
		dynScopedBufPtr->length = scopedpduHeaderOffset;
		
		//update the length for get response pduLenOffset 
		scoped_pdu_len_2.Val = (dynScopedBufPtr->length-3)-pduLenOffset;
		dynScopedBufPtr->length = pduLenOffset+1;
		Snmpv3BufferPut(scoped_pdu_len_2.v[1],dynScopedBufPtr);
		Snmpv3BufferPut(scoped_pdu_len_2.v[0],dynScopedBufPtr);
		dynScopedBufPtr->length = scopedpduHeaderOffset;

		scoped_pdu_len_1.Val = dynScopedBufPtr->length-4;
		if((scoped_pdu_len_1.Val >= 0x80) && (scoped_pdu_len_1.Val <= 0xFF))
		{// total scoped pdu length decreamented by 1
			dynScopedBufPtr->length = contextNameOffset+1;
			//if(snmpSecurityLevel>>1 & 0x01)
			//	Snmpv3BufferPut(0x04,dynScopedBufPtr);
			Snmpv3BufferPut(0x30,dynScopedBufPtr);
			Snmpv3BufferPut(0x81,dynScopedBufPtr);
			Snmpv3BufferPut(scoped_pdu_len_1.Val,dynScopedBufPtr);
			dynScopedBufPtr->length = scopedpduHeaderOffset;
			tempScopedData.head++;
			tempScopedData.length--;
		}
		else if((scoped_pdu_len_1.Val > 0xFF) && (scoped_pdu_len_1.Val < 0xFFFF))
		{			
			dynScopedBufPtr->length = contextNameOffset;
			Snmpv3BufferPut(0x30,dynScopedBufPtr);
			Snmpv3BufferPut(0x82,dynScopedBufPtr);
			Snmpv3BufferPut(scoped_pdu_len_1.v[1],dynScopedBufPtr);
			Snmpv3BufferPut(scoped_pdu_len_1.v[0],dynScopedBufPtr);
			dynScopedBufPtr->length = scopedpduHeaderOffset;
			//gSNMPv3ScopedPduResponseBuf.head++;
			//gSNMPv3ScopedPduResponseBuf.length--;
		}
		else
		{// total scoped pdu length decreamented by 2
			dynScopedBufPtr->length = contextNameOffset+2;
			Snmpv3BufferPut(0x30,dynScopedBufPtr);
			//Snmpv3BufferPut(0x81,dynScopedBufPtr);
			Snmpv3BufferPut(scoped_pdu_len_1.Val,dynScopedBufPtr);
			dynScopedBufPtr->length = scopedpduHeaderOffset;
			tempScopedData.head=tempScopedData.head+2;
			tempScopedData.length=tempScopedData.length-2;
		}


		//dynScopedBufPtr = &gSNMPv3ScopedPduResponseBuf;
		totalPdulength.Val = tempScopedData.length + \
							 gSNMPv3PduHeaderBuf.length + \
							 3; // asn_int+len+version

		if((snmpSecurityLevel & 0x02)==0x02)
		{
			tempPtr=tempBuf;
			*tempPtr++=0X04;
			if((tempScopedData.length >= 0x80) && (tempScopedData.length <= 0xFF))
			{
				*tempPtr++=0x81;
				*tempPtr=tempScopedData.length;
				tempCntr=3; //0x04(encrypted pkt),0x81,len
			}
			else if((tempScopedData.length > 0xFF) && (tempScopedData.length < 0xFFFF))
			{			
				*tempPtr++=0x82;
				*tempPtr++=tempScopedData.length>>8;
				*tempPtr=tempScopedData.length;
				tempCntr=4; //0x04(encrypted pkt),0x81,len_1,len_0
			}
			else
			{
				*tempPtr=tempScopedData.length;
				tempCntr=2; //0x04(encrypted pkt),len
			}
		}

		gSnmpV3OUTPduWholeMsgBuf.wholeMsgLen.Val=(totalPdulength.Val+tempCntr/*0x04,0x82,len_1,len_0*/);
		gSnmpV3OUTPduWholeMsgBuf.wholeMsgHead=(UINT8*)(malloc((size_t)gSnmpV3OUTPduWholeMsgBuf.wholeMsgLen.Val+4+16));
		if(gSnmpV3OUTPduWholeMsgBuf.wholeMsgHead == NULL)
			return FALSE;
		outBufPtr=gSnmpV3OUTPduWholeMsgBuf.wholeMsgHead;	


		//Start Writing to the outPut Buffer

		*outBufPtr++=STRUCTURE;

		totalPdulength.Val+=tempCntr;
							 
		if((totalPdulength.Val >= 0x80) && (totalPdulength.Val <= 0xFF))
		{
			*outBufPtr++=0x81;
			*outBufPtr++=totalPdulength.Val;
		}
		else if((totalPdulength.Val > 0xFF) && (totalPdulength.Val < 0xFFFF))
		{			
			*outBufPtr++=0x82;
			*outBufPtr++=totalPdulength.v[1];
			*outBufPtr++=totalPdulength.v[0];
		}
		else
			*outBufPtr++=totalPdulength.Val;

		*outBufPtr++=ASN_INT;
		*outBufPtr++=0x1;		
		*outBufPtr++=SNMP_V3;

		gSnmpV3OUTPduWholeMsgBuf.msgAuthParamOffsetOutWholeMsg=(UINT8*)(outBufPtr+gSNMPv3PduHeaderBuf.msgAuthParamOffset);
		//put global snmpv3 msg header 
		for(i=0;i<gSNMPv3PduHeaderBuf.length;i++)
		{
			*outBufPtr++=gSNMPv3PduHeaderBuf.head[i];
		}

		if (gSNMPv3PduHeaderBuf.head!=NULL)
		{	
			free(gSNMPv3PduHeaderBuf.head);
			gSNMPv3PduHeaderBuf.length=0x00;
			gSNMPv3PduHeaderBuf.head=NULL;
		}


		//Copy Scoped PDU to the Out Buffer
		if((snmpSecurityLevel & 0x02)==0x02) //Encrypted message	
		{
			//Copy Packet Auth indicator, length
			for(i=0;i<tempCntr;i++) 
			{
				*outBufPtr++=tempBuf[i];

			}
		}
		gSnmpV3OUTPduWholeMsgBuf.scopedPduOffset=outBufPtr;
		gSnmpV3OUTPduWholeMsgBuf.scopedPduStructLen=tempScopedData.length;

		i=0;
		*outBufPtr++=tempScopedData.head[i++];//0x30

		if(tempScopedData.head[1] == 0x81)
		{
			*outBufPtr++=tempScopedData.head[i++];//0x81
			*outBufPtr++=tempScopedData.head[i++];//len_0
		}
		else if(tempScopedData.head[1] == 0x82)
		{
			*outBufPtr++=tempScopedData.head[i++]; //0x82
			*outBufPtr++=tempScopedData.head[i++]; //len_1
			*outBufPtr++=tempScopedData.head[i++]; //len_0
		}
		else
			*outBufPtr++=tempScopedData.head[i++];//len_o
		
		// send context id and context name and the get response 
		// Authentication and privacy data packet will be sent from here onwards
		for(;i<(tempScopedData.length);i++)
		{
			*outBufPtr++=tempScopedData.head[i];
		}

		if(gSNMPv3ScopedPduResponseBuf.head != NULL)
		{
			free(gSNMPv3ScopedPduResponseBuf.head);
			gSNMPv3ScopedPduResponseBuf.length=0x00;
			gSNMPv3ScopedPduResponseBuf.head=NULL;
		}


		/*Encrypt the Response to the messgae originator*/
		if((snmpSecurityLevel & 0x02)==0x02) //Encrypted message
		{
			 /*Rxed SNMPv3 message is encrypted. Hence Response should be encrypted*/
			 gSnmpV3OUTPduWholeMsgBuf.wholeMsgLen.Val = outBufPtr-gSnmpV3OUTPduWholeMsgBuf.wholeMsgHead;
			 /*If user privacy protocol is AES*/
			if(Snmpv3AESEncryptResponseScopedPdu(&gSnmpV3OUTPduWholeMsgBuf) != SNMPV3_MSG_PRIV_PASS)
				return SNMPV3_MSG_PRIV_FAIL;
		
			/*If user privacy Protocol is DES*/
			//snmpV3DESDecryptRxedScopedPdu();
		}

		/* Authenticate the whole message to be transmitted*/
		if((snmpSecurityLevel & 0x01)==0x01) //Authenticatd message
		{
			 /*Rxed SNMPv3 message is Authenticated.Send authenticatin parameters for the Response*/
			gSnmpV3OUTPduWholeMsgBuf.wholeMsgLen.Val = outBufPtr-gSnmpV3OUTPduWholeMsgBuf.wholeMsgHead;
			 /*If user authentication is HAMC-MD5-96*/
			if(Snmpv3AuthenticateTxPduForDataIntegrity(&gSnmpV3OUTPduWholeMsgBuf)!=SNMPV3_MSG_AUTH_PASS)
				return SNMPV3_MSG_AUTH_FAIL;

			tempPtr = outBufPtr;
			outBufPtr=gSnmpV3OUTPduWholeMsgBuf.msgAuthParamOffsetOutWholeMsg;
			for(i=0;i<snmpOutMsgAuthParamLen;i++)
				*outBufPtr++=snmpOutMsgAuthParamStrng[i];
			outBufPtr = tempPtr;
		}
			
		gSnmpV3OUTPduWholeMsgBuf.wholeMsgLen.Val = outBufPtr-gSnmpV3OUTPduWholeMsgBuf.wholeMsgHead;
		outBufPtr=gSnmpV3OUTPduWholeMsgBuf.wholeMsgHead;
		for(i=0;i < gSnmpV3OUTPduWholeMsgBuf.wholeMsgLen.Val;i++)
		{	
			_SNMPPut(*(outBufPtr+i));
		}

		//if(gSNMPv3ScopedPduResponseBuf.head != NULL)
		if(gSnmpV3OUTPduWholeMsgBuf.wholeMsgHead != NULL)
		{
			free(gSnmpV3OUTPduWholeMsgBuf.wholeMsgHead);
			gSnmpV3OUTPduWholeMsgBuf.wholeMsgHead=0x00;
			gSnmpV3OUTPduWholeMsgBuf.wholeMsgLen.Val=0x00;
			gSnmpV3OUTPduWholeMsgBuf.snmpMsgHead = NULL;
			gSnmpV3OUTPduWholeMsgBuf.msgAuthParamOffsetOutWholeMsg = NULL;
			gSnmpV3OUTPduWholeMsgBuf.scopedPduOffset =  NULL;			
		}

	}
	return TRUE;
}


/****************************************************************************
  Function:
	BOOL Snmpv3IsValidInt(DWORD* val)
	
  Summary:
  	Verifies variable datatype as INT and retrieves its value.

  Description:
  	This routine populates and validates the received variable for the
  	data type as "ASN_INT" and the data length for max 4 bytes.
  	This rotuine only refers to the incoming snmpv3 request dynamically 
	allocated 	memory buffer 'gSNMPv3ScopedPduRequestBuf' .
  	
  	 		 		  	
  Precondition:
	None
	
  Parameters:
  	val - Pointer to memory where int var value will be stored.
 
  ReturnValues:
	TRUE	- If valid integer type and value is received.
	FALSE	- Other than integer data type and value received .
	
  Remarks:
	None.
***************************************************************************/
BOOL Snmpv3IsValidInt(DWORD* val)
{
	DWORD_VAL tempData;
    UINT8	tempLen=0;

    
    // Get variable type
    if (!IS_ASN_INT(Snmpv3GetBufferData(gSNMPv3ScopedPduRequestBuf,++gSNMPv3ScopedPduDataPos)))
        return FALSE;

	// Integer length of more than 32-bit is not supported.
	tempLen = Snmpv3GetBufferData(gSNMPv3ScopedPduRequestBuf,++gSNMPv3ScopedPduDataPos);
    if ( tempLen > 4u)
        return FALSE;
    

    tempData.Val = 0;
    while( tempLen-- )
        tempData.v[tempLen] = Snmpv3GetBufferData(gSNMPv3ScopedPduRequestBuf,
        													++gSNMPv3ScopedPduDataPos);

    *val = tempData.Val;

    return TRUE;
}


/****************************************************************************
  Function:
	BOOL _Snmpv3IsValidInt(UINT8 * wholeMsgPtr,WORD* pos, DWORD* val )
	
  Summary:
  	Verifies variable datatype as INT and retrieves its value.

  Description:
  	This routine populates and validates the received variable for the
  	data type as "ASN_INT" and the data length for max 4 bytes.
  	 		 		  	
  Precondition:
	None
	
  Parameters:
  	wholeMsgPtr - Pointer to memory where int var value is be stored.
 	pos - position in the memory buffer where data taype to be varified is stored
 	val - Pointer to memory where int var value will be stored.
 	
  ReturnValues:
	TRUE	- If valid integer type and value is received.
	FALSE	- Other than integer data type and value received .
	
  Remarks:
	None.
***************************************************************************/

BOOL _Snmpv3IsValidInt(UINT8 * wholeMsgPtr,WORD* pos, DWORD* val )
{
	DWORD_VAL tempData;
    UINT8	tempLen=0;

	UINT8* lclWholeMsgPtr;
	
	lclWholeMsgPtr=wholeMsgPtr;

    
    // Get variable type
    if (!IS_ASN_INT(Snmpv3GetWholeMsgBufferData(lclWholeMsgPtr,pos)))
        return FALSE;

	// Integer length of more than 32-bit is not supported.
	tempLen = Snmpv3GetWholeMsgBufferData(lclWholeMsgPtr,pos);
    if ( tempLen > 4u)
        return FALSE;
    

    tempData.Val = 0;
    while( tempLen-- )
        tempData.v[tempLen] = Snmpv3GetWholeMsgBufferData(lclWholeMsgPtr,pos);

    *val = tempData.Val;

    return TRUE;
}

/****************************************************************************
  Function:
	BOOL IsSNMPv3ValidStructure(WORD* dataLen)
	
  Summary:
  	Decode variable length structure.

  Description:
	This routine is used  to verify whether the received varbind is of type
	STRUCTURE and to find out the variable binding structure length.
	This rotuine only refers to the incoming snmpv3 request dynamically 
	allocated 	memory buffer 'gSNMPv3ScopedPduRequestBuf' .
  	
  Precondition:
	ProcessHeader() is called.	
	
  Parameters:
  	datalen	- Pointer to memory to store OID structure length.
 
  Return Values:
	TRUE	- If valid Structure data type and value is received.
	FALSE	- If variable data structure is not type STRUCTURE. 	

  Remarks:
	None.
***************************************************************************/
BOOL IsSNMPv3ValidStructure(WORD* dataLen)
{
    DWORD_VAL tempLen;

    if ( !IS_STRUCTURE(Snmpv3GetBufferData(gSNMPv3ScopedPduRequestBuf,++gSNMPv3ScopedPduDataPos)) )
        return FALSE;

	tempLen.Val = Snmpv3GetBufferData(gSNMPv3ScopedPduRequestBuf,++gSNMPv3ScopedPduDataPos);
    if ( tempLen.Val == 0x81) 
    {
        tempLen.Val = Snmpv3GetBufferData(gSNMPv3ScopedPduRequestBuf,++gSNMPv3ScopedPduDataPos);
    }
	else if(tempLen.Val == 0x82)
	{
        tempLen.v[1] = Snmpv3GetBufferData(gSNMPv3ScopedPduRequestBuf,++gSNMPv3ScopedPduDataPos);		
        tempLen.v[0] = Snmpv3GetBufferData(gSNMPv3ScopedPduRequestBuf,++gSNMPv3ScopedPduDataPos);
	}
	else if(tempLen.Val == 0)
		return FALSE;
    // Since we are using UDP as our transport and UDP are not fragmented,
    // this structure length cannot be more than 1500 bytes.
    // As a result, we will only use lower WORD of length value.
    *dataLen = tempLen.Val;

    return TRUE;
}


/****************************************************************************
  Function:
	BOOL _IsSNMPv3ValidStructure(UINT8* wholeMsgPtr,UINT16* pos, WORD* dataLen )
	
  Summary:
  	Decode variable length structure.

  Description:
  	This routine populates and validates the received variable for the
  	data type as "STRUCTURE" and the data length for max 4 bytes.
  	 		 		  	
  Precondition:
	None
	
  Parameters:
  	wholeMsgPtr - Pointer to memory where int var value is be stored.
 	pos - position in the memory buffer where data taype to be varified is stored
 	val - Pointer to memory where int var value will be stored.
 	
  ReturnValues:
	TRUE	- If valid integer type and value is received.
	FALSE	- Other than integer data type and value received .
	
  Remarks:
	None.
***************************************************************************/
BOOL _IsSNMPv3ValidStructure(UINT8* wholeMsgPtr,UINT16* pos, WORD* dataLen )
{
    DWORD_VAL tempLen;

    if ( !IS_STRUCTURE(Snmpv3GetWholeMsgBufferData(wholeMsgPtr,pos)) )
        return FALSE;


	tempLen.Val = Snmpv3GetWholeMsgBufferData(wholeMsgPtr,pos);
    if ( tempLen.Val == 0x81) 
    {
        tempLen.Val = Snmpv3GetWholeMsgBufferData(wholeMsgPtr,pos);
    }
	else if(tempLen.Val == 0x82)
	{
        tempLen.v[1] = Snmpv3GetWholeMsgBufferData(wholeMsgPtr,pos);		
        tempLen.v[0] = Snmpv3GetWholeMsgBufferData(wholeMsgPtr,pos);
	}
	else if(tempLen.Val == 0)
		return FALSE;
    // Since we are using UDP as our transport and UDP are not fragmented,
    // this structure length cannot be more than 1500 bytes.
    // As a result, we will only use lower WORD of length value.
    *dataLen = tempLen.Val;

    return TRUE;
}


/****************************************************************************
  Function:
	static BYTE FindOIDsFromSnmpV3Request(WORD pdulen)
	
  Summary:
  	Finds number of varbinds in the varbind list received in a SNMPv3 pdu.
  	
  Description:
  	This routine is used to find the number of OIDs requested in the received
  	snmp pdu.   	
  	
  Precondition	:
	ProcessVariables() is called.	
		
  Parameters:
	pdulen		-	Length of snmp pdu request received. 
    
  Return Values:
	varCount	-	Number of OIDs found in a pdu request. 
	
  Remarks:
  	None.
  	
***************************************************************************/
static BYTE FindOIDsFromSnmpV3Request(WORD pdulen)
{
BYTE varCount=0;
WORD prevUDPRxOffset;
WORD varBindLen;
WORD snmpPduLen;
 	
	snmpPduLen=pdulen;

	prevUDPRxOffset=gSNMPv3ScopedPduDataPos;

	while(snmpPduLen)
	{
		
		if(!IsSNMPv3ValidStructure(&varBindLen))
			return FALSE;

		gSNMPv3ScopedPduDataPos = gSNMPv3ScopedPduDataPos+varBindLen;
		varCount++;
		snmpPduLen=snmpPduLen
					-1      //  1   byte for STRUCTURE identifier
					-1  //  1  byte for varbind length 
					-varBindLen;
		
	}

	gSNMPv3ScopedPduDataPos=prevUDPRxOffset;

	return varCount;
}


/****************************************************************************
  Function:
	void Snmpv3ReportPdu(SNMPV3MSGDATA *dynScopedBufPtr)
	
  Summary:
  	Constructs the report pdu infomration for the Report Pdu.
  	
  Description:
  	The SNMPv3 PDU exchange starts with the agent sending a report pdu on 
  	reception of any Get_Request PDU for SNMPv3 request. 
  	This routine froms the report pdu for response to the requesting entity.
  	
  Precondition	:
	ProcessVariables() is called and a valid SNMPv3 request is received. 
		
  Parameters:
	dynScopedBufPtr	- pointer to the response buffer memory where the 'report' response 
					   to be savced for transmission. 
    
  Return Values:
	None
	
  Remarks:
  	None.
  	
***************************************************************************/
void Snmpv3ReportPdu(SNMPV3MSGDATA *dynScopedBufPtr)
{
	BYTE	usmStatEngineIds[]={43,6,1,6,3,15,1,1,4,0};
	BYTE	reportPduLenOffset=0;	
	BYTE	usmLen=0,i=0;
	UINT16	varbindPairOffset1=0;
	

	Snmpv3BufferPut(STRUCTURE,dynScopedBufPtr);
	varbindPairOffset1 = dynScopedBufPtr->length;
	Snmpv3BufferPut(0,dynScopedBufPtr);

/* put  usm OID */
	Snmpv3BufferPut(ASN_OID,dynScopedBufPtr);
	usmLen = sizeof(usmStatEngineIds);
	Snmpv3BufferPut(usmLen,dynScopedBufPtr);
	while(usmLen--)
		Snmpv3BufferPut(usmStatEngineIds[i++],dynScopedBufPtr);

/* put engine ID stat value */	
	Snmpv3BufferPut(SNMP_COUNTER32,dynScopedBufPtr);
	Snmpv3BufferPut(4,dynScopedBufPtr);
	Snmpv3BufferPut(gUsmStatsEngineID.v[3],dynScopedBufPtr);
	Snmpv3BufferPut(gUsmStatsEngineID.v[2],dynScopedBufPtr);
	Snmpv3BufferPut(gUsmStatsEngineID.v[1],dynScopedBufPtr);
	Snmpv3BufferPut(gUsmStatsEngineID.v[0],dynScopedBufPtr);
	
	reportPduLenOffset = dynScopedBufPtr->length;
	
	usmLen = dynScopedBufPtr->length - (varbindPairOffset1+1) ;
	dynScopedBufPtr->length = varbindPairOffset1;
	Snmpv3BufferPut(usmLen,dynScopedBufPtr);
	
	dynScopedBufPtr->length = reportPduLenOffset;
	
	
}


/****************************************************************************
  Function:
	BOOL IsSnmpv3ValidOID(BYTE* oid, BYTE* len)
	
  Summary:
  	Populates OID type, length and oid string from the received pdu.

  Description:
	In this routine, OID data type "ASN_OID" is verified in the received pdu.
	If the data type is matched, then only var bind is processed. OID length
	and OID is populated. The max OID length can be 15. 
  	
  Precondition:
	ProcessVariabels() is called.
	
  Parameters:
  	oid - Pointer to memory to store the received OID string
  	len	- Pointer to memory to store OID length
 
  Return Values:
	TRUE	- If value type is ASN_OID and oid length not more than 15. 
	FALSE	- Otherwise.
	
  Remarks:
	None.
***************************************************************************/
static BOOL IsSnmpv3ValidOID(BYTE* oid, BYTE* len)
{
    BYTE tempLen=0;

    // Fetch and verify that this is OID.
    if ( !IS_OID(Snmpv3GetBufferData(gSNMPv3ScopedPduRequestBuf,++gSNMPv3ScopedPduDataPos)) )
        return FALSE;

   tempLen = Snmpv3GetBufferData(gSNMPv3ScopedPduRequestBuf,++gSNMPv3ScopedPduDataPos);

    // Make sure that OID length is within our capability.
    if (tempLen > (BYTE)OID_MAX_LEN )
        return FALSE;

    *len = tempLen;

	while( tempLen-- )
	{
       *oid++ = Snmpv3GetBufferData(gSNMPv3ScopedPduRequestBuf,++gSNMPv3ScopedPduDataPos);
	}
	*oid=0xff;
    return TRUE;
}

/****************************************************************************
  Function:
	static BOOL IsSnmpV3ASNNull(void)
	
  Summary:
  	Verifies the value type as ASN_NULL.

  Description:
  	For Get,Get_Next,Get_Bulk snmp reuest, the var bind the value data type 
  	should be ASN_NULL and value field must be NULL and . This routine
  	verifies the data type and value fields in the received requests.
  	The SET request, the value data type can not be ASN_NULL,
  	otherwise the snmp request is not processed.
  	This rotuine only refers to the incoming snmpv3 request dynamically 
	allocated 	memory buffer 'gSNMPv3ScopedPduRequestBuf' .

  Precondition:
	None
	
  Parameters:
  	None
 
  Returns Values
	TRUE	- If value type is ASN_NULL and value is NULL. 
	FALSE	- If data type and value is other than ASN_NULL and NULL resp.
	
  Remarks:
	None.
***************************************************************************/
static BOOL IsSnmpV3ASNNull(void)
{
	BYTE a;

	a = Snmpv3GetBufferData(gSNMPv3ScopedPduRequestBuf,++gSNMPv3ScopedPduDataPos);

	if (!IS_ASN_NULL(a))
			return FALSE;

    // Fetch and verify that length value is zero.
    return (Snmpv3GetBufferData(gSNMPv3ScopedPduRequestBuf,++gSNMPv3ScopedPduDataPos) == 0u );
}


/****************************************************************************
  Function:
	void Snmpv3SetErrorStatus(WORD errorStatusOffset,
                           WORD errorIndexOffset,
                           SNMP_ERR_STATUS errorStatus,
                           BYTE errorIndex,SNMPV3MSGDATA *dynScopedPduPutBuf)
  Summary:
  	Set snmpv3 error status in the response pdu. 
  	
  Description:
  	This routine processes the received snmp Get request pdu for the 
  	variable binding in the request and also creates the response pdu.
  	
  Precondition:
	ProcessVariables() is called.	
	
  Parameters:
    errorStatusOffset - Offset to update error status in Response Tx pdu 	
    errorIndexOffset  - Offset to update error index
    errorStatus		  - Snmp process error to be updated in response.	
    errorIndex		  - Index of the request varbind in the var bind list 
    					for which error status is to be updated. 					
    dynScopedPduPutBuf -  dynamic snmpv3 scoped pdu buffer
  Returns:
	None.
	
  Remarks:
  	None.
***************************************************************************/
void Snmpv3SetErrorStatus(WORD errorStatusOffset,
                           WORD errorIndexOffset,
                           SNMP_ERR_STATUS errorStatus,
                           BYTE errorIndex,SNMPV3MSGDATA *dynScopedPduPutBuf)
{
    WORD prevOffset;

    prevOffset = dynScopedPduPutBuf->length;
	dynScopedPduPutBuf->length = errorStatusOffset;
    Snmpv3BufferPut(errorStatus,dynScopedPduPutBuf);

    
	dynScopedPduPutBuf->length = errorIndexOffset;
    Snmpv3BufferPut(errorIndex,dynScopedPduPutBuf);

	dynScopedPduPutBuf->length = prevOffset;
}

/****************************************************************************
  Function:
	BYTE Snmpv3IsValidAuthStructure(WORD* dataLen)
	
  Summary:
  	Decode variable length structure.

  Description:
	This routine is used  to verify whether the received varbind is of type
	STRUCTURE and to find out the variable binding structure length.
  	
  Precondition:
	ProcessHeader() is called.	
	
  Parameters:
  	datalen	- Pointer to memory to store OID structure length.
 
  Return Values:
	headrbytes	- Variable binding length.
	FALSE		- If variable data structure is not type STRUCTURE. 	

  Remarks:
	None.
***************************************************************************/
BYTE Snmpv3IsValidAuthStructure(WORD* dataLen)
{
    DWORD_VAL tempLen;
    BYTE headerBytes;
	BYTE authStructure=0;

	authStructure = _SNMPGet();

    if ( !IS_STRUCTURE(authStructure) && !IS_SNMPV3_AUTH_STRUCTURE(authStructure) )
        return FALSE;

    // Retrieve structure length
    headerBytes = IsValidLength(&tempLen.w[0]);
    if ( !headerBytes )
        return FALSE;

    headerBytes++;

    // Since we are using UDP as our transport and UDP are not fragmented,
    // this structure length cannot be more than 1500 bytes.
    // As a result, we will only use lower WORD of length value.
    *dataLen = tempLen.w[0];

    return headerBytes;
}

/****************************************************************************
  Function:
	BYTE _Snmpv3IsValidAuthStructure(WORD* dataLen)
	
  Summary:
  	Decode variable length structure.

  Description:
	This routine is used  to verify whether the received varbind is of type
	STRUCTURE and to find out the variable binding structure length.
  	This rotuine only refers to the incoming snmpv3 request dynamically 
	allocated   memory buffer 'gSnmpV3InPduWholeMsgBuf' .

  Precondition:
	ProcessHeader() is called.	
	
  Parameters:
  	datalen	- Pointer to memory to store OID structure length.
 
  Return Values:
	headrbytes	- Variable binding length.
	FALSE		- If variable data structure is not type STRUCTURE. 	

  Remarks:
	None.
***************************************************************************/

BYTE _Snmpv3IsValidAuthStructure(WORD* dataLen)
{
    WORD_VAL tempLen;
    BYTE headerBytes;
	BYTE authStructure=0;
	UINT16 tempPos;
	
	BYTE tempData;
	
	tempPos=snmpMsgBufSeekPos;
	authStructure = Snmpv3GetWholeMsgBufferData(gSnmpV3InPduWholeMsgBuf.snmpMsgHead,&tempPos);
	

    if ( !IS_STRUCTURE(authStructure) && !IS_SNMPV3_AUTH_STRUCTURE(authStructure) )
        return FALSE;

	
    // Initialize length value.
    tempLen.Val = 0;
    headerBytes = 0;

    tempData = Snmpv3GetWholeMsgBufferData(gSnmpV3InPduWholeMsgBuf.snmpMsgHead,&tempPos);
    tempLen.v[0] = tempData;
    if ( tempData & 0x80 )
    {
        tempData &= 0x7F;

        // We do not support any length byte count of more than 2
        // i.e. total length value must not be more than 16-bit.
        if ( tempData > 2u )
            return FALSE;

        // Total length bytes are 0x80 itself plus tempData.
        headerBytes = tempData + 1;

        // Get upto 2 bytes of length value.
        while( tempData-- )
            tempLen.v[tempData] = Snmpv3GetWholeMsgBufferData(gSnmpV3InPduWholeMsgBuf.snmpMsgHead,&tempPos);
    }
    else
        headerBytes = 1;

	 if ( !headerBytes )
      return FALSE;

	gSnmpV3InPduWholeMsgBuf.scopedPduAuthStructVal=authStructure;
	gSnmpV3InPduWholeMsgBuf.scopedPduStructLen=tempLen.Val;
	
    headerBytes++;

    // Since we are using UDP as our transport and UDP are not fragmented,
    // this structure length cannot be more than 1500 bytes.
    // As a result, we will only use lower WORD of length value.
    *dataLen = tempLen.Val;

	snmpMsgBufSeekPos=tempPos;
    return headerBytes;
}


#if defined(SNMP_V1_V2_TRAP_WITH_SNMPV3)
UINT8 gSNMPV3TrapSecurityLevel = NO_REPORT_NO_PRIVACY_NO_AUTH;
#define INVALID_INDEX 0xFF

/****************************************************************************
  Function:
	BYTE Snmpv3GetUserIndxFromUsmUserDB(BYTE targetIndex)
	
  Summary:
  	Routine to find the index of the user name in the user data base table. 
  	
  Description:
  	There are two different data base tables defined with SNMPv3 stack,
  	like 'snmpV3UserDataBase' and 'gSnmpv3TrapConfigData'.
	It returns the index of the user name which matches to the trap target 
	user name within the user data base. 

  Precondition:
	Trap notification event is triggred and the trap send flag is enabled.
	
  Parameters:
  	targetIndex -index of the 'gSnmpv3TrapConfigData' table to match the 
  			     'userSecurityName' with the user data base  
 
  Return Values:
	INVALID_INDEX - if the trap target user name does not match.
	BYTE - Byte value fo the index matched

  Remarks:
	None.
***************************************************************************/
BYTE Snmpv3GetUserIndxFromUsmUserDB(BYTE targetIndex)
{
	UINT8 *userSecurityName=NULL;
	UINT8 userDBsecurityLevel=0;
	UINT8 trapSecurityLevel=0; 
	UINT8 userTrapSecLen=0;
	UINT8 *userTrapSecurityName=NULL;
	UINT8 i=0;

	trapSecurityLevel = Snmpv3GetTrapSecurityLevel((STD_BASED_SNMPV3_SECURITY_LEVEL)gSnmpv3TrapConfigData[targetIndex].securityLevelType);
	if(trapSecurityLevel == INVALID_MSG)
		return INVALID_INDEX;

	for(i=0;i<SNMPV3_USM_MAX_USER;i++)
	{
		userSecurityName = snmpV3UserDataBase[i].userName;
		userDBsecurityLevel = Snmpv3GetSecurityLevel(i);
		userTrapSecLen = strlen(gSnmpv3TrapConfigData[targetIndex].userSecurityName);
		userTrapSecurityName = gSnmpv3TrapConfigData[targetIndex].userSecurityName;
		
		if(userTrapSecLen != snmpV3UserDataBase[i].userNameLength)
			continue;
		if(strncmp(userTrapSecurityName,userSecurityName,userTrapSecLen) == 0)
		{
			if(trapSecurityLevel == userDBsecurityLevel)
				return i;
			else
				continue;
		}
	}

	return INVALID_INDEX;
}


/****************************************************************************
  Function:
	BOOL Snmpv3CmprTrapSecNameAndSecLvlWithUSMDb(
				BYTE tragetIndex,
				BYTE userTrapSecLen,
				UINT8 *userTrapSecurityName,
				STD_BASED_SNMPV3_SECURITY_LEVEL securityLevel)
	
  Summary:
  	Routine to find the index of the user name in the user data base table. 
  	
  Description:
  	There are two different data base tables defined with SNMPv3 stack,
  	like 'snmpV3UserDataBase' and 'gSnmpv3TrapConfigData'.
	This routine is used to validte the trap user security level setting with
	SET request.
	

  Precondition:
	SET operation would be allowed if the USM security conditions and
	user security name in the request is matched to one of the user security 
	name stored in the usm user database.
	
  Parameters:
  	targetIndex -index of the 'gSnmpv3TrapConfigData' table to match the 
  			     'userSecurityName' with the user data base  
	userTrapSecLen - user sec name length in the SET request
	userTrapSecurityName - pointer to user sec name in the SET request
	securityLevel - trap security level to be SET on the agent
 
  Return Values:
	TRUE - if the trap target user sec level setting is successful
	FLASE - If the SET failed due to non matching of the security parameters

  Remarks:
	None.
***************************************************************************/
BOOL Snmpv3CmprTrapSecNameAndSecLvlWithUSMDb(BYTE tragetIndex,BYTE userTrapSecLen,
								UINT8 *userTrapSecurityName,STD_BASED_SNMPV3_SECURITY_LEVEL securityLevel)
{

	UINT8 *userSecurityName=NULL;
	UINT8 userDBsecurityLevel=0;
	UINT8 trapSecurityLevel=0; 
	UINT8 i=0;

	trapSecurityLevel = Snmpv3GetTrapSecurityLevel(securityLevel);
	if(trapSecurityLevel == INVALID_MSG)
		return FALSE;

	for(i=0;i<SNMPV3_USM_MAX_USER;i++)
	{
		userSecurityName = snmpV3UserDataBase[i].userName;
		userDBsecurityLevel = Snmpv3GetSecurityLevel(i);
		if(userTrapSecLen != snmpV3UserDataBase[i].userNameLength)
			continue;
		if(strncmp(userTrapSecurityName,userSecurityName,userTrapSecLen) == 0)
		{
			if(trapSecurityLevel == userDBsecurityLevel)
				return TRUE;
			else
				continue;
		}
	}

	return FALSE;
}


/****************************************************************************
  Function:
	BYTE Snmpv3GetTrapSecurityLevel(STD_BASED_SNMPV3_SECURITY_LEVEL securityLevel)
	
  Summary:
  	Routine to find the report, auth and privacy flags settings in the TRAP. 
  	
  Description:
  	This routine to find the report, auth and privacy flags setting for the trap to be 
  	generated. The message flags octet's least significant three bits: 
  	Reportable, PrivFlag, AuthFlag forms different secuity level combinations.
	

  Precondition:
	None
	
  Parameters:
  	securityLevel -trap security level to be compared for getting the agent's security 
  				level settings 
  Return Values:
	NO_REPORT_NO_PRIVACY_NO_AUTH - No authentication, no encryption
	NO_REPORT_NO_PRIVACY_BUT_AUTH_PROVIDED - authentication but no encryption
  	NO_REPORT_PRIVACY_AND_AUTH_PROVIDED - authentication and encryption 
  	INVALID_MSG - if security level doesn't match any of the above

  Remarks:
	None.
***************************************************************************/
BYTE Snmpv3GetTrapSecurityLevel(STD_BASED_SNMPV3_SECURITY_LEVEL securityLevel)
{
	BYTE tempSecurityLevel=0xFF;
	
	switch(securityLevel)
	{
		case NO_AUTH_NO_PRIV:
			tempSecurityLevel =  NO_REPORT_NO_PRIVACY_NO_AUTH;
			break;
		case AUTH_NO_PRIV:
			tempSecurityLevel = NO_REPORT_NO_PRIVACY_BUT_AUTH_PROVIDED;
			break;
		case AUTH_PRIV:
			tempSecurityLevel = NO_REPORT_PRIVACY_AND_AUTH_PROVIDED;
			break;
		default:
			return INVALID_MSG;
	}
	return tempSecurityLevel;
}
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
